armor66/LoRa-E77-GNSS/PCB/tBeacon_D2_mount.jpg

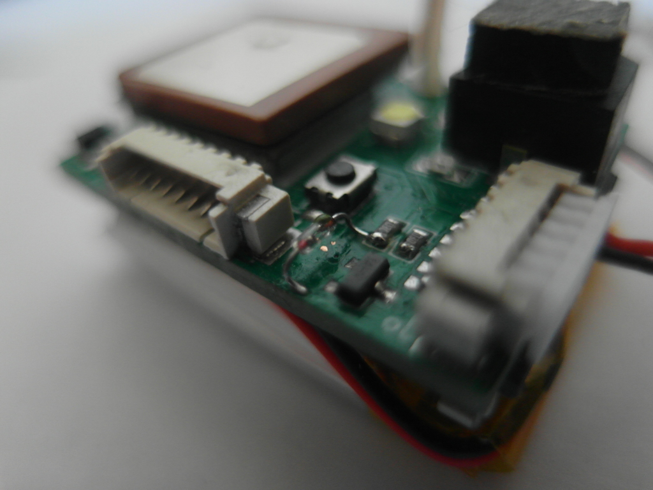
PCB/tBeacon_D2_mount.jpg
