armor66/LoRa-E77-GNSS/Photos/1.jpg

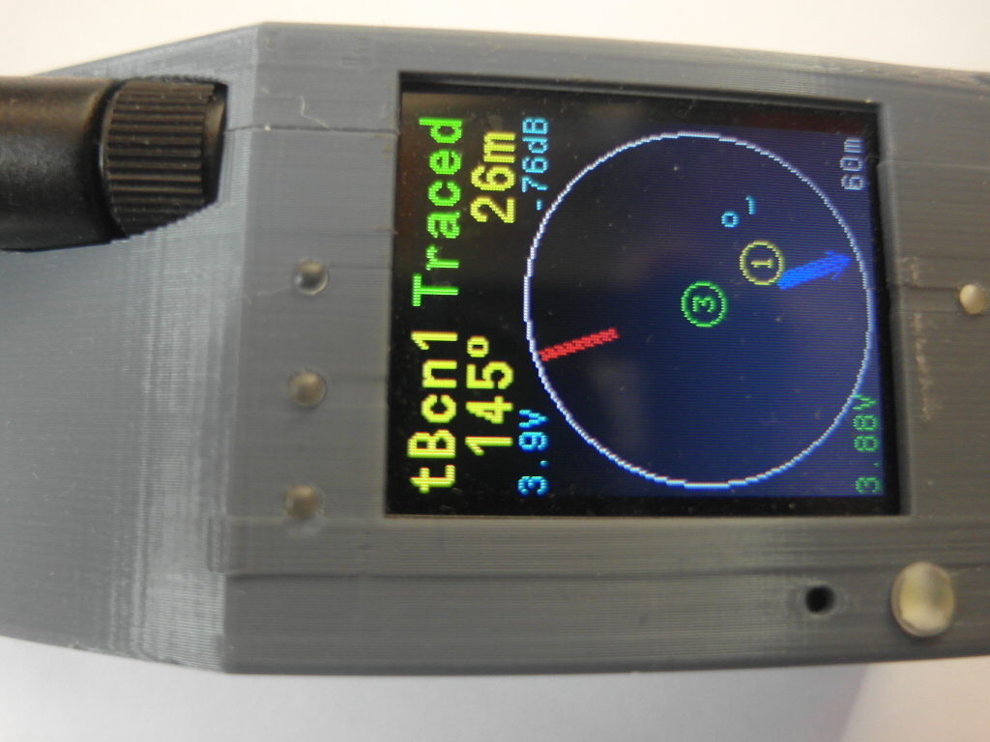
Photos/1.jpg
