armor66/LoRa-E77-GNSS/Photos/GPIO_Beacon.png

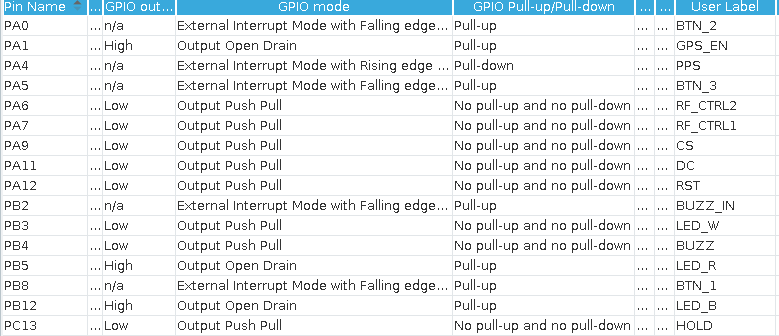
Photos/GPIO_Beacon.png
