armor66/LoRa-E77-GNSS/Photos/QUESCAN.jpg

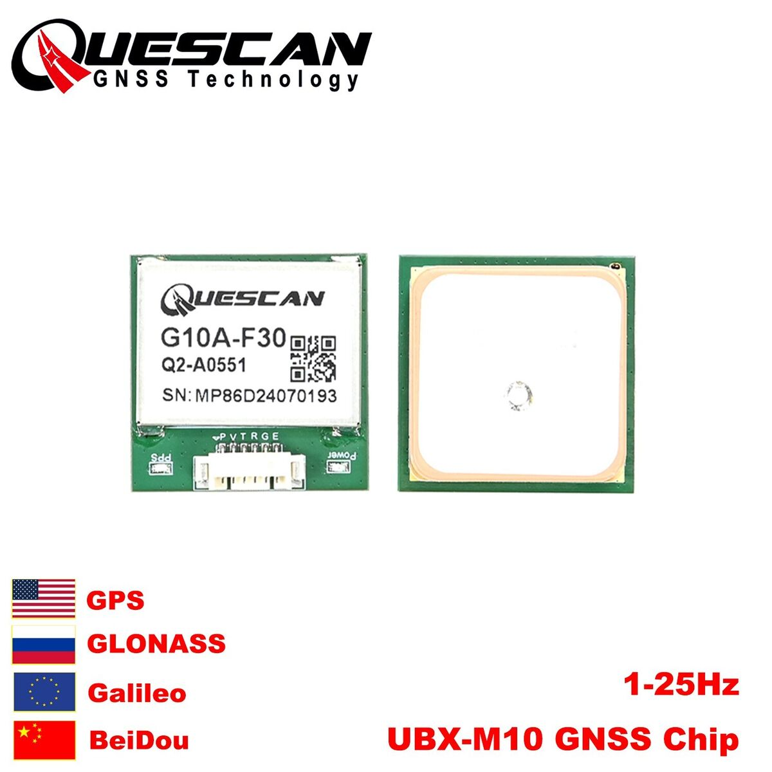
Photos/QUESCAN.jpg
