armor66/LoRa-E77-GNSS/E77-128x160/Core/Src/menu.c

#include <stdio.h>			//for 'sprintf'
#include <math.h>
#include "main.h"
#include "gpio.h"
#include "menu.h"
#include "buttons.h"
#include "tim.h"
#include "lptim.h"
#include "settings.h"
#include "compass.h"
#include "gnss.h"
#include "lrns.h"
#include "ds3231.h"

#include "lcd_display.h"

#define START_POS_GROUP		6

uint8_t get_current_item(void);
uint8_t get_last_item(void);
void set_current_item(uint8_t new_value);
void reset_current_item_in_menu(uint8_t menu);

void scroll_up(void);
void scroll_down(void);
void switch_forward(void);
void switch_backward(void);
// MAIN MENU
void draw_main(void);
//void main_ok(void);
// NAVIGATION MENU
//SUB NAVIGATION MENU
void draw_navigation(void);
void draw_beacons(void);
void navigation_up(void);
void navigation_down(void);
void navigation_ok(void);
//void navigation_esc(void);
void beacons_ok(void);
void beacons_esc(void);

void draw_navto_points(void);
void navto_points_ok(void);
void navto_points_esc(void);

// LAPS MENU
void draw_laps(void);
void new_laps(void);
void continue_laps(void);
// DEVICES MENU
void draw_devices(void);
void draw_this_device(void);
void draw_device_submenu(void);
void draw_set_points(void);
//SUB DEVICES MENU
void scroll_devices_up(void);
void scroll_devices_down(void);
void devices_ok(void);
void devices_esc(void);
// POINTS MENU
void draw_points(void);
void points_esc(void);
void draw_show_points(void);
void draw_clear_group(void);
void confirm_clear_group(void);
void draw_save_group(void);
void confirm_save_group(void);
void decline_save_group(void);
//SUB POINTS MENU
void set_subpoint_up(void);
void set_subpoint_down(void);
void set_subpoint_ok(void);
void set_subpoint_esc(void);
// SETTINGS MENU
void draw_settings(void);
void draw_set_settings(void);
//SUB SETTINGS MENU :0
void set_device_number_up(void);
void set_device_number_down(void);
void set_device_number_ok(void);
void set_device_number_esc(void);
//:1
void set_spreading_factor_up(void);
void set_spreading_factor_down(void);
void set_spreading_factor_ok(void);
void set_spreading_factor_esc(void);
//:2
void set_coding_rate_up(void);
void set_coding_rate_down(void);
void set_coding_rate_ok(void);
void set_coding_rate_esc(void);
//:3
void set_freq_channel_up(void);
void set_freq_channel_down(void);
void set_freq_channel_ok(void);
void set_freq_channel_esc(void);
//:4
void set_tx_power_up(void);
void set_tx_power_down(void);
void set_tx_power_ok(void);
void set_tx_power_esc(void);
//:5
void set_timezone_up(void);
void set_timezone_down(void);
void set_timezone_ok(void);
void set_timezone_esc(void);
//:6
void set_timeout_up(void);
void set_timeout_down(void);
void set_timeout_ok(void);
void set_timeout_esc(void);
//:7
void set_fence_up(void);
void set_fence_down(void);
void set_fence_ok(void);
void set_fence_esc(void);

// SAVE SETTINGS
void draw_confirm_settings(void);
void confirm_settings_reboot(void);
void donot_save_settings(void);
void confirm_erase_points(void);
void confirm_settings_restore(void);
//ACTIONS MENU
void draw_actions(void);
void power_long(void);
void actions_ok(void);
void actions_esc(void);
void draw_erase_points(void);
void draw_restore_defaults(void);

void draw_binding(void);
void confirm_binding(void);
void exit_binding(void);
void device_up(void);
void device_down(void);

void set_brightness(void);

//ALL MENUS HERE
enum    //menu number starts from 1, because 0 is used as "end marker" in menu structs
{
    M_MAIN = 1,
    M_NAVIGATION,
	M_BEACONS,

	M_LAPS,
	M_DEVICES,
	M_DEVICE_SUBMENU,
	M_SET_POINTS,

	M_NAVTO_POINTS,

	M_POINTS,
	M_POINTS_SUBMENU,
	M_CONFIRM_CLEARGROUP,
	M_CONFIRM_SAVEGROUP,

	M_SETTINGS,
	M_CONFIRM_SETTINGS,

	M_SET_DEVICE_NUMBER,
	M_SET_SPREADING_FACTOR,
	M_SET_CODING_RATE,
    M_SET_FREQ_CHANNEL,
    M_SET_TX_POWER,
	M_SET_TIMEZONE,
	M_SET_TIMEOUT,
	M_SET_FENCE,

	M_ACTIONS,
	M_ERASE_POINTS,
	M_CONFIRM_RESTORING,
	M_BINDING
};

//ALL MENU ITEMS HERE (for each menu separately)
//note: for all menus first item always has index of 0
#define M_ALL_I_FIRST (0)
//MAIN
enum
{
    M_MAIN_I_NAVIGATION = 0,
	M_MAIN_I_DEVICES,
	M_MAIN_I_NAVTO_POINTS,
	M_MAIN_I_POINTS,
	M_MAIN_I_SETTINGS,
	M_MAIN_I_ACTIONS,					//last item
    M_MAIN_I_LAST = M_MAIN_I_ACTIONS	//copy last item here
};
//DEVICE TO SAVE SUBMENU
enum
{
	M_DEVICE_SUBMENU_I_ALARMS = 0,
	M_DEVICE_SUBMENU_I_GROUP1,
	M_DEVICE_SUBMENU_I_GROUP2,
	M_DEVICE_SUBMENU_I_GROUP3,
	M_DEVICE_SUBMENU_I_GROUP4,
	M_DEVICE_SUBMENU_I_GROUP5,
	M_DEVICE_SUBMENU_I_BCNMAN,
	M_DEVICE_SUBMENU_I_LAST = M_DEVICE_SUBMENU_I_BCNMAN
};
//POINTS
enum
{
	M_POINTS_I_ALARMS = 0,
	M_POINTS_I_GROUP1,
	M_POINTS_I_GROUP2,
	M_POINTS_I_GROUP3,
	M_POINTS_I_GROUP4,
	M_POINTS_I_GROUP5,
	M_POINTS_I_BCNMAN,
	M_POINTS_I_SAVED1,
	M_POINTS_I_SAVED2,
	M_POINTS_I_SAVED3,
	M_POINTS_I_SAVED4,
	M_POINTS_I_SAVED5,
	M_POINTS_I_LAST = M_POINTS_I_SAVED5
};
//SETTINGS
enum
{
    M_SETTINGS_I_DEVICE = 0,
	M_SETTINGS_I_SPREADING_FACTOR,
	M_SETTINGS_I_CODING_RATE,
	M_SETTINGS_I_FREQ_CHANNEL,
	M_SETTINGS_I_TX_POWER,
	M_SETTINGS_I_TIMEZONE,
	M_SETTINGS_I_TIMEOUT,
	M_SETTINGS_I_FENCE,
    M_SETTINGS_I_LAST = M_SETTINGS_I_FENCE
};
//ACTIONS SUBMENU
enum
{
	M_ACTIONS_I_POWER_OFF = 0,
    M_ACTIONS_I_EMERGENCY,
	M_ACTIONS_I_ANTITHEFT,
	M_ACTIONS_I_BCNHALT,
	M_ACTIONS_I_BEEPER,
	M_ACTIONS_I_ERASE_POINTS,
	M_ACTIONS_I_SET_DEFAULTS,
	M_ACTIONS_I_FLWTREK,						//last item
	M_ACTIONS_I_LAST = M_ACTIONS_I_FLWTREK		//copy last item here
};
//Only exclusive (non default) actions here, for example edit a variable in settings
const struct
{
    uint8_t current_menu;
    uint8_t button_pressed;
    void (*execute_function)(void);
} menu_exclusive_table[] =
{
//  Current Menu                Button pressed          Action (function name)
//	{M_MAIN,					BTN_OK,					main_ok},
	{M_MAIN,					BTN_ESC,				set_brightness},

	{M_NAVIGATION,				BTN_UP,					navigation_up},		//change distance range
	{M_NAVIGATION,				BTN_DOWN,				navigation_down},	//change distance range
	{M_NAVIGATION,				BTN_OK,					navigation_ok},		//other points on loop
//	{M_NAVIGATION,				BTN_ESC,				navigation_esc},	//to main menu

	{M_BEACONS,					BTN_UP,					navigation_up},
	{M_BEACONS,					BTN_DOWN,				navigation_down},
	{M_BEACONS,					BTN_OK,					beacons_ok},
	{M_BEACONS,					BTN_ESC,				beacons_esc},

	{M_LAPS,					BTN_UP,					new_laps},
	{M_LAPS,					BTN_DOWN,				continue_laps},
	{M_LAPS,					BTN_OK,					draw_devices},
//	{M_LAPS,					BTN_ESC,				to M_MAIN},			//default action

	{M_DEVICES,					BTN_UP,					scroll_devices_up},
	{M_DEVICES,					BTN_DOWN,				scroll_devices_down},
	{M_DEVICES,					BTN_OK,					devices_ok},
	{M_DEVICES,					BTN_ESC,				devices_esc},

	{M_SET_POINTS,				BTN_UP,                 set_subpoint_up},
	{M_SET_POINTS,				BTN_DOWN,               set_subpoint_down},
	{M_SET_POINTS,				BTN_OK,                 set_subpoint_ok},
	{M_SET_POINTS,				BTN_ESC,            	set_subpoint_esc},

	{M_NAVTO_POINTS,			BTN_UP,					navigation_up},
	{M_NAVTO_POINTS,			BTN_DOWN,				navigation_down},
	{M_NAVTO_POINTS,			BTN_OK,					navto_points_ok},
	{M_NAVTO_POINTS,			BTN_ESC,				navto_points_esc},

	{M_SET_DEVICE_NUMBER,		BTN_UP,                 set_device_number_up},
	{M_SET_DEVICE_NUMBER,		BTN_DOWN,               set_device_number_down},
	{M_SET_DEVICE_NUMBER,		BTN_OK,                 set_device_number_ok},
	{M_SET_DEVICE_NUMBER,		BTN_ESC,            	set_device_number_esc},

	{M_SET_SPREADING_FACTOR,	BTN_UP,                 set_spreading_factor_up},
	{M_SET_SPREADING_FACTOR,	BTN_DOWN,               set_spreading_factor_down},
	{M_SET_SPREADING_FACTOR,	BTN_OK,                 set_spreading_factor_ok},
	{M_SET_SPREADING_FACTOR,	BTN_ESC,            	set_spreading_factor_esc},

	{M_SET_CODING_RATE,			BTN_UP,                 set_coding_rate_up},
	{M_SET_CODING_RATE,			BTN_DOWN,               set_coding_rate_down},
	{M_SET_CODING_RATE,			BTN_OK,                 set_coding_rate_ok},
	{M_SET_CODING_RATE,			BTN_ESC,            	set_coding_rate_esc},

	{M_SET_FREQ_CHANNEL,		BTN_UP,                 set_freq_channel_up},
	{M_SET_FREQ_CHANNEL,		BTN_DOWN,               set_freq_channel_down},
	{M_SET_FREQ_CHANNEL,		BTN_OK,                 set_freq_channel_ok},
	{M_SET_FREQ_CHANNEL,		BTN_ESC,            	set_freq_channel_esc},

	{M_SET_TX_POWER,			BTN_UP,                 set_tx_power_up},
	{M_SET_TX_POWER,			BTN_DOWN,               set_tx_power_down},
	{M_SET_TX_POWER,			BTN_OK,                 set_tx_power_ok},
	{M_SET_TX_POWER,			BTN_ESC,                set_tx_power_esc},

	{M_SET_TIMEZONE,			BTN_UP,					set_timezone_up},
	{M_SET_TIMEZONE,			BTN_DOWN,				set_timezone_down},
	{M_SET_TIMEZONE,			BTN_OK,					set_timezone_ok},
	{M_SET_TIMEZONE,			BTN_ESC,				set_timezone_esc},

	{M_SET_TIMEOUT,				BTN_UP,                 set_timeout_up},
	{M_SET_TIMEOUT,				BTN_DOWN,               set_timeout_down},
	{M_SET_TIMEOUT,				BTN_OK,                 set_timeout_ok},
	{M_SET_TIMEOUT,				BTN_ESC,            	set_timeout_esc},

	{M_SET_FENCE,				BTN_UP,                 set_fence_up},
	{M_SET_FENCE,				BTN_DOWN,               set_fence_down},
	{M_SET_FENCE,				BTN_OK,                 set_fence_ok},
	{M_SET_FENCE,				BTN_ESC,            	set_fence_esc},
	{M_CONFIRM_SETTINGS,		BTN_OK,					confirm_settings_reboot},
	{M_CONFIRM_SETTINGS,		BTN_ESC,				donot_save_settings},

	{M_MAIN,					BTN_PWR_LONG,			power_long},
	{M_NAVIGATION,				BTN_PWR_LONG,			power_long},
	{M_LAPS,					BTN_PWR_LONG,			power_long},
	{M_BEACONS,					BTN_PWR_LONG,			power_long},
	{M_DEVICES,					BTN_PWR_LONG,			power_long},
	{M_NAVTO_POINTS,			BTN_PWR_LONG,			power_long},
	{M_POINTS,					BTN_PWR_LONG,			power_long},
	{M_POINTS,					BTN_ESC,				points_esc},
	{M_POINTS_SUBMENU,			BTN_OK,					draw_clear_group},
	{M_CONFIRM_CLEARGROUP,		BTN_OK,					confirm_clear_group},
	{M_CONFIRM_SAVEGROUP,		BTN_UP,					set_subpoint_up},
	{M_CONFIRM_SAVEGROUP,		BTN_DOWN,				set_subpoint_down},
	{M_CONFIRM_SAVEGROUP,		BTN_OK,					confirm_save_group},
	{M_CONFIRM_SAVEGROUP,		BTN_ESC,				decline_save_group},
	{M_ACTIONS,					BTN_PWR_LONG,			power_long},
	{M_ACTIONS,					BTN_OK,					actions_ok},
	{M_ACTIONS,					BTN_ESC,				actions_esc},
//
	{M_ERASE_POINTS,			BTN_OK,					confirm_erase_points},
	{M_CONFIRM_RESTORING,		BTN_OK,					confirm_settings_restore},
	{M_BINDING,					BTN_UP,					device_up},
	{M_BINDING,					BTN_DOWN,				device_down},
	{M_BINDING,					BTN_OK,					confirm_binding},
	{M_BINDING,					BTN_ESC,				exit_binding},
    {0, 0, 0}   //end marker
};

//Default behavior (non exclusive) when OK button has been pressed (move forward)
const struct
{
    uint8_t current_menu;
    uint8_t current_item;
    uint8_t next_menu;
} menu_forward_table[] =
{
//  Current Menu                Current Item                		Next Menu
	{M_MAIN,  				M_MAIN_I_NAVIGATION,		M_NAVIGATION},
	{M_MAIN,    			M_MAIN_I_DEVICES,			M_LAPS},
//	{M_MAIN,    			M_MAIN_I_DEVICES,			M_DEVICES},
	{M_MAIN,    			M_MAIN_I_NAVTO_POINTS,		M_NAVTO_POINTS},
	{M_MAIN,    			M_MAIN_I_POINTS,			M_POINTS},
	{M_MAIN,    			M_MAIN_I_SETTINGS,			M_SETTINGS},
	{M_MAIN,    			M_MAIN_I_ACTIONS,			M_ACTIONS},

	{M_DEVICE_SUBMENU,		M_DEVICE_SUBMENU_I_ALARMS,			M_SET_POINTS},
	{M_DEVICE_SUBMENU,		M_DEVICE_SUBMENU_I_GROUP1,			M_SET_POINTS},
	{M_DEVICE_SUBMENU,		M_DEVICE_SUBMENU_I_GROUP2,			M_SET_POINTS},
	{M_DEVICE_SUBMENU,		M_DEVICE_SUBMENU_I_GROUP3,			M_SET_POINTS},
	{M_DEVICE_SUBMENU,		M_DEVICE_SUBMENU_I_GROUP4,	 		M_SET_POINTS},
	{M_DEVICE_SUBMENU,		M_DEVICE_SUBMENU_I_GROUP5,			M_SET_POINTS},
	{M_DEVICE_SUBMENU,		M_DEVICE_SUBMENU_I_BCNMAN,			M_SET_POINTS},

	{M_POINTS,				M_POINTS_I_ALARMS,				M_POINTS_SUBMENU},
	{M_POINTS,				M_POINTS_I_GROUP1,				M_POINTS_SUBMENU},
	{M_POINTS,				M_POINTS_I_GROUP2,			 	M_POINTS_SUBMENU},
	{M_POINTS,				M_POINTS_I_GROUP3,				M_POINTS_SUBMENU},
	{M_POINTS,				M_POINTS_I_GROUP4,				M_POINTS_SUBMENU},
	{M_POINTS,				M_POINTS_I_GROUP5,				M_POINTS_SUBMENU},
	{M_POINTS,				M_POINTS_I_BCNMAN,				M_POINTS_SUBMENU},
	{M_POINTS,				M_POINTS_I_SAVED1,				M_POINTS_SUBMENU},
	{M_POINTS,				M_POINTS_I_SAVED2,				M_POINTS_SUBMENU},
	{M_POINTS,				M_POINTS_I_SAVED3,				M_POINTS_SUBMENU},
	{M_POINTS,				M_POINTS_I_SAVED4,				M_POINTS_SUBMENU},
	{M_POINTS,				M_POINTS_I_SAVED5,				M_POINTS_SUBMENU},

	{M_SETTINGS,			M_SETTINGS_I_DEVICE,				M_SET_DEVICE_NUMBER},
	{M_SETTINGS,			M_SETTINGS_I_SPREADING_FACTOR,		M_SET_SPREADING_FACTOR},
	{M_SETTINGS,			M_SETTINGS_I_CODING_RATE,			M_SET_CODING_RATE},
	{M_SETTINGS,			M_SETTINGS_I_FREQ_CHANNEL,			M_SET_FREQ_CHANNEL},
	{M_SETTINGS,			M_SETTINGS_I_TX_POWER,				M_SET_TX_POWER},
	{M_SETTINGS,			M_SETTINGS_I_TIMEZONE,				M_SET_TIMEZONE},
	{M_SETTINGS,			M_SETTINGS_I_TIMEOUT,				M_SET_TIMEOUT},
	{M_SETTINGS,			M_SETTINGS_I_FENCE,					M_SET_FENCE},
    {0, 0, 0}   //end marker
};

//Default behavior (non exclusive) when ESC button has been pressed (move backward)
const struct
{
    uint8_t current_menu;
    uint8_t next_menu;
} menu_backward_table[] =
{
//  Current Menu                Next Menu
    {M_NAVIGATION,              M_MAIN},
	{M_BEACONS,					M_NAVIGATION},

	{M_LAPS,					M_MAIN},
	{M_DEVICES,                 M_MAIN},
	{M_DEVICE_SUBMENU,			M_DEVICES},
	{M_SET_POINTS,				M_DEVICE_SUBMENU},

	{M_NAVTO_POINTS,	        M_MAIN},

	{M_POINTS,	                M_MAIN},
	{M_POINTS_SUBMENU,			M_POINTS},
	{M_CONFIRM_CLEARGROUP,		M_POINTS_SUBMENU},
	{M_CONFIRM_SAVEGROUP,		M_NAVTO_POINTS},
//	{M_POINTS_SUBMENU_DEVICES,	M_POINTS},

    {M_SETTINGS,                M_CONFIRM_SETTINGS},	//M_MAIN},
	{M_CONFIRM_SETTINGS,		M_SETTINGS},
    {M_SET_DEVICE_NUMBER,       M_SETTINGS},
	{M_SET_SPREADING_FACTOR,	M_SETTINGS},
	{M_SET_CODING_RATE,			M_SETTINGS},
	{M_SET_FREQ_CHANNEL,		M_SETTINGS},
	{M_SET_TX_POWER,			M_SETTINGS},
	{M_SET_TIMEZONE,	        M_SETTINGS},
	{M_SET_TIMEOUT,				M_SETTINGS},
	{M_SET_FENCE,				M_SETTINGS},

	{M_ERASE_POINTS,			M_ACTIONS},
	{M_CONFIRM_RESTORING,		M_ACTIONS},
	{M_BINDING,					M_ACTIONS},
    {0, 0}      //end marker
};
//Structure with list of menus and real-time values of current item in current menu. Last Item is needed for scroll function
//note: if current menu has no items (like INFO menu) no need to put it in structure below,
//because item functions (get, get last, set) automatically return 0 (which is zero item)
struct
{
    const uint8_t curent_menu;
    uint8_t cur_item;
    const uint8_t last_item;
} item_table[] =
{
//  Current Menu                Current Item                Last Item in Current Menu
    {M_MAIN,                    M_ALL_I_FIRST,              M_MAIN_I_LAST},
	{M_DEVICE_SUBMENU,			M_ALL_I_FIRST,				M_DEVICE_SUBMENU_I_LAST},
	{M_POINTS, 	                M_ALL_I_FIRST,              M_POINTS_I_LAST},
    {M_SETTINGS,                M_ALL_I_FIRST,              M_SETTINGS_I_LAST},
	{M_ACTIONS,					M_ALL_I_FIRST,				M_ACTIONS_I_LAST},
    {0, 0, 0}   //end marker
};

//List of menus with appropriate functions to draw it (show on screen)
const struct
{
    uint8_t current;
    void (*action)(void);
} menu_draw_table[] =
{
//  Current Menu                Draw Function
	{M_MAIN,                    draw_main},

	{M_NAVIGATION,				draw_navigation},
	{M_BEACONS,					draw_beacons},

	{M_LAPS,                 	draw_laps},
	{M_DEVICES,                 draw_devices},			//can be commented
	{M_DEVICE_SUBMENU,     		draw_device_submenu},
	{M_SET_POINTS,				draw_set_points},

	{M_NAVTO_POINTS,			draw_navto_points},

	{M_POINTS,                  draw_points},
	{M_POINTS_SUBMENU,			draw_show_points},
	{M_CONFIRM_SAVEGROUP,		draw_save_group},

    {M_SETTINGS,                draw_settings},
    {M_SET_DEVICE_NUMBER,		draw_set_settings},
	{M_SET_SPREADING_FACTOR,	draw_set_settings},
	{M_SET_CODING_RATE,			draw_set_settings},
	{M_SET_FREQ_CHANNEL,		draw_set_settings},
	{M_SET_TX_POWER,			draw_set_settings},
    {M_SET_TIMEZONE,			draw_set_settings},
	{M_SET_TIMEOUT,				draw_set_settings},
	{M_SET_FENCE,				draw_set_settings},
	{M_CONFIRM_SETTINGS,		draw_confirm_settings},

	{M_ACTIONS,					draw_actions},
	{M_ERASE_POINTS,			draw_erase_points},
	{M_CONFIRM_RESTORING,		draw_restore_defaults},
	{M_BINDING,					draw_binding},
    {0, 0}      //end mark
};

//#define PVTsize 100
//uint8_t PVTbuffer[PVTsize] = {0};
char string_buffer[20][27];		//15raws,22(~240:11)items
char *fixType[] = {"NoFix", "DReck", "2DFix", "3DFix", "DReck", "Time"}; 	//only 2 bits used to transmit (first 4 items)

//int8_t main_flags.current_point_group = 0;		//Current number of memory point to save
uint8_t current_mem_subpoint = 0;
uint8_t points_group_ind = 0;						//NavTo Points begins from Start Positions group
uint8_t memory_subpoint = 0;
uint8_t memory_subpoint_ind[MEMORY_POINT_GROUPS];
uint8_t flag_group_has_changed[MEMORY_POINT_GROUPS];

int16_t north = 0;
int16_t north_old = 0;
int16_t azimuth_relative_deg = 0;
int16_t scaled_dist;
int16_t distance_old[10];
double north_rad = 0;
double north_rad_old = 0;
double azimuth_relative_rad;
double azimuth_relative_rad_old[10];

int8_t row;
int8_t this_device;								//device number of this device, see init_menu()
//int8_t current_device;

int8_t current_menu;
uint8_t return_from_power_menu; 							//Menu to return to after exit from power menu. Power menu can be accessed from different menus, therefore we have to store menu to return.
uint8_t return_from_points_menu;
uint8_t flag_settings_changed = 0;

uint8_t *p_coding_rate_values;
uint8_t *p_tx_power_values;

uint16_t range = 30;
uint8_t range_ind = 0;
uint8_t range_scale[] = {1, 2, 4, 8, 16, 32, 64};

int8_t previous_menu;		//to return if start point not saved
int8_t firstFreeStartPoint;	//for save_start_pos()
int8_t ind = 0;				//out of the function draw_navto_points() to roll up if points > 3
int8_t startHour;
int8_t startMinute;
int8_t startSecond;
int8_t lapsSaved;
int8_t lapsPaused;
int8_t lapsCounter;
uint16_t lapsTimeSaved;
uint16_t lapsDistSaved;

struct devices_struct **pp_devices_menu;
struct point_groups_struct **pp_point_groups_menu;
struct points_struct **pp_points_menu;

struct settings_struct *p_settings_menu;
struct settings_struct settings_copy_menu;

ds3231_time_t *p_timeData;

void init_menu(void)
{
	//Load all devices
	pp_devices_menu = get_devices();
	pp_point_groups_menu = get_point_groups();
	pp_points_menu = get_points();
	//Load settings and create a local copy
	p_settings_menu = get_settings();
	settings_copy_menu = *p_settings_menu;
	main_flags.binding_device = main_flags.current_device = this_device = p_settings_menu->device_number;

	p_coding_rate_values = get_coding_rate_values();
	p_tx_power_values = get_tx_power_values();

	p_timeData = get_timeData();

	current_menu = M_MAIN;
//	return_from_power_menu = M_MAIN;
	set_current_item(M_MAIN_I_NAVIGATION);

	main_flags.display_status = 1;
	main_flags.update_screen = 1;
	main_flags.brightness = 16;
	lptim1_start(16, main_flags.brightness);
/* first position to save when first_time_locked after power on */
	memory_subpoint_ind[START_POS_GROUP] = 1;
	main_flags.binding_sf = p_settings_menu->spreading_factor;
}

void set_brightness(void)
{
	if(main_flags.brightness == 16)
	{
		main_flags.brightness = 11;
	}else if(main_flags.brightness == 11)
	{
		main_flags.brightness = 0;
	}else
	{
		main_flags.brightness = 16;
	}
	lptim1_start(16, main_flags.brightness);
}

//Check for buttons and change menu if needed
void change_menu(uint8_t button_code)
{
	if((current_menu == M_LAPS) && (lapsCounter) && (button_code > 2))	//should respond any except BTN_PWR
	{
		lptim1_start(16, main_flags.brightness);
		main_flags.display_status = 1;
	}

	int8_t point_absolute_index = 0;
	if(main_flags.display_status)	//if lcd is on
	{	//search for exclusive operation(function) for this case
		for (uint8_t i = 0; menu_exclusive_table[i].current_menu; i++)     //until end marker
		{
			if (current_menu == menu_exclusive_table[i].current_menu &&
				button_code == menu_exclusive_table[i].button_pressed)
			{
				fill_screen(BLACK);
				menu_exclusive_table[i].execute_function();
				return;         //exit
			}
		}
//there is no exclusive operations for that case, perform default action
		switch (button_code)
		{
			case BTN_UP:
				scroll_up();
				break;

			case BTN_DOWN:
				scroll_down();
				break;

			case BTN_OK:
				switch_forward();
				fill_screen(BLACK);
				break;

			case BTN_ESC:
				switch_backward();
				fill_screen(BLACK);
				break;

			case BTN_PWR:
				lptim1_stop();							//lcd_off
				main_flags.display_status = 0;			//do not draw or change menu
				main_flags.current_point_group = 0;		//to start save or erase points from group 1
				break;

			default:
				break;
		}	//switch (button_code)
	}else 	//if lcd is off, display_status = 0
	{
		switch (button_code)
		{
			case BTN_PWR_LONG:
				lptim1_start(16, main_flags.brightness);
				main_flags.display_status = 1;
				if(current_menu == M_NAVIGATION && pp_devices_menu[this_device]->valid_fix_flag && pp_devices_menu[this_device]->flwtrek_flag)
				{
					main_flags.find_nearest_trekpoint_flag = 1;		//find_nearest_trekpoint();
					fill_screen(BLACK);
				}
				break;

			case BTN_UP:				//if short pressed
				timer16_start();		//hold 1.5 second for next short press

				if(main_flags.current_point_group < 5) {
					main_flags.current_point_group++;
					memory_subpoint_ind[main_flags.current_point_group] = 0;	//to start from point 1
//					led_blue_on();		//main_flags.current_point_group has set
				}else {
					shortBeeps(2);			//if(main_flags.current_point_group == 5)
					main_flags.current_point_group = 0;
//					led_blue_off();		//main_flags.current_point_group has reseted
				}
				break;		//leave case BTN_UP

			case BTN_OK:			//if long pressed && (main_flags.current_point_group > 0))
				timer16_stop();		//stop before IRQ and clear current_point_group

				if(!pp_devices_menu[this_device]->valid_fix_flag) {
					shortBeeps(2);			//if no valid_fix_flag when attempt to save point
					main_flags.current_point_group = 0;
//					led_blue_off();		//main_flags.current_point_group has reseted
					break;		//leave case BTN_OK
				}
				if(main_flags.current_point_group > 0) {
					longBeeps(main_flags.current_point_group);
				}else break;	//leave case BTN_OK

				do{
					memory_subpoint_ind[main_flags.current_point_group]++;
					if(memory_subpoint_ind[main_flags.current_point_group] == MEMORY_SUBPOINTS)
					{
						memory_subpoint_ind[main_flags.current_point_group] = 0;							//exist_flag always == 0
						pp_points_menu[main_flags.current_point_group * MEMORY_SUBPOINTS]->exist_flag = 0;	//clear subpoint 0
					}
					point_absolute_index = main_flags.current_point_group * MEMORY_SUBPOINTS + memory_subpoint_ind[main_flags.current_point_group];
				} while (pp_points_menu[point_absolute_index]->exist_flag);		// == 1

				if(memory_subpoint_ind[main_flags.current_point_group] == 0)
				{
					main_flags.current_point_group = 0;
//					led_blue_off();		//main_flags.current_point_group has reseted
					break;			//longBeeps(main_flags.current_point_group) and leave case BTN_OK
				}

				save_one_point(point_absolute_index);
				points_group_save(main_flags.current_point_group);

				shortBeeps(1);	//memory_subpoint_ind[main_flags.current_point_group]);	//number of point to save

				fill_screen(BLACK);
//				return_from_points_menu = current_menu;
				current_menu = M_POINTS;
				set_current_item(main_flags.current_point_group);
				main_flags.current_point_group = 0;
//				led_blue_off();		//main_flags.current_point_group has reseted
				break;		//leave case BTN_OK

			case BTN_DOWN:				//if short pressed
				timer16_start();		//hold 1.5 second for next short press

				if(main_flags.current_point_group < 7) {			//5 groups + beacon + 1 for all devices
					main_flags.current_point_group++;
//					led_blue_on();		//main_flags.current_point_group has set
				}else {
					shortBeeps(2);			//if(main_flags.current_point_group == 12)
					main_flags.current_point_group = 0;
//					led_blue_off();		//main_flags.current_point_group has reseted
				}
				break;		//leave case BTN_DOWN

			case BTN_ESC:		//if long pressed && (main_flags.current_point_group > 0))
				timer16_stop();		//stop before IRQ and clear current_point_group

				if(main_flags.current_point_group > 0)
				{
					longBeeps(main_flags.current_point_group);
//					shortBeeps(1);							//just for notice instead of actual long beeps
				}else break;	//leave case BTN_ESC

				if(main_flags.current_point_group < 7)			//5 groups + beacon
				{
/*as in "confirm_clear_group(void)" function*/
					clear_points_group(main_flags.current_point_group);
					int8_t ind;
					for(uint8_t sub_point = 0; sub_point < MEMORY_SUBPOINTS; sub_point++)
					{
						ind = (main_flags.current_point_group * MEMORY_SUBPOINTS) + sub_point;
						pp_points_menu[ind]->exist_flag = 0;
					}
					saved_group_load(main_flags.current_point_group);
				}

				if(main_flags.current_point_group == 7)			//for all devices
				{
					erase_saved_devices();

					for(uint8_t i = 57; i < 96; i++)	//57 to 96: 8 for saved device each
					{
						pp_points_menu[i]->exist_flag = 0;
					}

					for(uint8_t i = 1; i < (DEVICES_ON_AIR_MAX+1); i++)
					{
						lost_device_load(i);
					}
				}

/******************************************/
				fill_screen(BLACK);
//				return_from_points_menu = current_menu;
				current_menu = M_POINTS;
				set_current_item(main_flags.current_point_group);
				main_flags.current_point_group = 0;
//				led_blue_off();		//main_flags.current_point_group has reseted
				break;		//leave case BTN_ESC

			default:
				main_flags.current_point_group = 0;
//				led_blue_off();		//main_flags.current_point_group has reseted
				break;
		}	//switch (button_code)
	}		//if lcd is off
}	//change_menu
//Scroll current menu Up
void scroll_up(void)
{
    uint8_t current = get_current_item();
    uint8_t last = get_last_item();

    if (current == M_ALL_I_FIRST)
    {
        set_current_item(last);
    }
    else
    {
        set_current_item(current - 1);
    }
}
//Scroll current menu Down
void scroll_down(void)
{
    uint8_t current = get_current_item();
    uint8_t last = get_last_item();

    if (current == last)
    {
        set_current_item(M_ALL_I_FIRST);
    }
    else
    {
        set_current_item(current + 1);
    }
}
//Switch menu forward by default
void switch_forward(void)
{
    for (uint8_t i = 0; menu_forward_table[i].current_menu; i++)
    {
        if (current_menu == menu_forward_table[i].current_menu &&
            get_current_item() == menu_forward_table[i].current_item)
        {
            current_menu = menu_forward_table[i].next_menu;
            break;
        }
    }
}
//Switch menu backward by default
void switch_backward(void)
{
    for (uint8_t i = 0; menu_backward_table[i].current_menu; i++)
    {
        if (current_menu == menu_backward_table[i].current_menu)
        {
            set_current_item(M_ALL_I_FIRST);        //reset current item before exit
            current_menu = menu_backward_table[i].next_menu;
            break;
        }
    }
}
//Get currently selected item in current menu
uint8_t get_current_item(void)
{
    for (uint8_t i = 0; item_table[i].curent_menu; i++)
    {
        if (current_menu == item_table[i].curent_menu)
        {
            return item_table[i].cur_item;
        }
    }
    return 0;       //automatically return 0 if item not found in item_table[]
}
//Get last item in current menu
uint8_t get_last_item(void)
{
    for (uint8_t i = 0; item_table[i].curent_menu; i++)
    {
        if (current_menu == item_table[i].curent_menu)
        {
            return item_table[i].last_item;
        }
    }
    return 0;       //automatically return 0 if item not found in item_table[]
}
//Set item to be current in current menu
void set_current_item(uint8_t new_value)
{
    for (uint8_t i = 0; item_table[i].curent_menu; i++)
    {
        if (current_menu == item_table[i].curent_menu)
        {
            item_table[i].cur_item = new_value;
            break;
        }
    }
}
//Reset item in any menu
void reset_current_item_in_menu(uint8_t menu)
{
    for (uint8_t i = 0; item_table[i].curent_menu; i++)
    {
        if (menu == item_table[i].curent_menu)
        {
            item_table[i].cur_item = M_ALL_I_FIRST;
            break;
        }
    }
}
//------------------------------------------------------------------
//--------------------------- DRAW -----------------------------
//Draw current menu
void draw_current_menu(void)
{
	if(main_flags.display_status)	//if lcd is on
	{
		for (uint8_t i = 0; menu_draw_table[i].current; i++)
		{
			if (current_menu == menu_draw_table[i].current)
			{
				menu_draw_table[i].action();
				break;
			}
		}
	}
//	else if(!IS_BEACON)	//if display has not lit, if IS_BEACON do nothing
//	{
		for(int8_t i = 1; i < 1 + p_settings_menu->devices_on_air; i++)
		{
			if(i != this_device)
			{
				if(pp_devices_menu[i]->emergency_flag)	// || pp_devices_menu[i]->antitheft_flag)
				{
//					fill_screen(BLACK);
					lptim1_start(16, main_flags.brightness);
					main_flags.display_status = 1;
//todo go to alarm point while display_status==0
//					points_group_ind = 0;
//					draw_navto_points();			//to draw immediately
//					current_menu = M_NAVTO_POINTS;	//do not return previous menu
				}
			}
		}
//	}
}
//------------------------------------------------------------------
//---------------------------MAIN MENU------------------------------

void draw_main(void)
{
	uint8_t day;	// = PVTbuffer[7+6];
//	uint8_t month = PVTbuffer[6+6];
	uint8_t year;	// = (PVTbuffer[5+6]<<8) + PVTbuffer[4+6];
	int8_t hour;	// = PVTbuffer[14];
	row = 0;

	if(main_flags.rtc_enabled || main_flags.fix_valid)
//(pp_devices_menu[this_device]->valid_date_flag)	//bit 5: information about UTC Date and Time of Day validity conﬁrmation is available
	{
		year = (uint8_t)(p_timeData->year - 2000);
		hour = p_timeData->hour + p_settings_menu->time_zone_hour;
		if(hour > 23)
		{
			hour = hour - 24;
			day = 1 + p_timeData->date;
		}
		else day = p_timeData->date;
	}
	else day = year = hour = 0;

	if(pp_devices_menu[this_device]->batt_voltage < 50)		// U < 3.2volt (!pp_devices_menu[this_device]->batt_voltage)
	{
		sprintf(&string_buffer[row][0], "DevID:%02d Batt low!", this_device);
		draw_str_by_rows(0, 1+row*11, &string_buffer[row][0], &Font_7x9, ORANGE,BLACK);
	}else
	{
		sprintf(&string_buffer[row][0], "DevID:%d/%d %d.%02dVolt", this_device, p_settings_menu->devices_on_air,
			(pp_devices_menu[this_device]->batt_voltage+270)/100,
			(pp_devices_menu[this_device]->batt_voltage+270)%100);
		draw_str_by_rows(0, 1+row*11, &string_buffer[row][0], &Font_7x9, WHITE,BLACK);
	}
	row+=1;	//1
	if(main_flags.rtc_enabled || main_flags.fix_valid)
	{
		(sprintf(&string_buffer[row][0], "%02d/%02d/%02d  %02d:%02d:%02d",
			day, p_timeData->month, year, hour, p_timeData->minute, p_timeData->second));
		(main_flags.fix_valid)?
				draw_str_by_rows(0, 1+row*11, &string_buffer[row][0], &Font_7x9, WHITE,BLACK):
				draw_str_by_rows(0, 1+row*11, &string_buffer[row][0], &Font_7x9, CYAN,BLACK);
	}else
	{
		(sprintf(&string_buffer[row][0], "RTC IS NOT APPLIED"));
		draw_str_by_rows(0, 1+row*11, &string_buffer[row][0], &Font_7x9, ORANGE,BLACK);
	}
//	for (uint8_t k = 0; k < row+1; k++)
//	{
//		draw_str_by_rows(0, 1+k*11, &string_buffer[k][0], &Font_7x9, WHITE,BLACK);
//	}
	row+=1;	//2
	if(main_flags.nav_pvt_ram_flag)
	{
		sprintf(&string_buffer[row][0], "%d %5s pDop:%2d.%02d", main_flags.fix_valid, fixType[pp_devices_menu[this_device]->fix_type_opt],
						pp_devices_menu[this_device]->p_dop/100, pp_devices_menu[this_device]->p_dop%100);
		(pp_devices_menu[this_device]->valid_fix_flag)?
				draw_str_by_rows(0, 1+row*11, &string_buffer[row][0], &Font_7x9, WHITE,BLACK):
//				draw_str_by_rows(0, 1+row*11, &string_buffer[row][0], &Font_7x9, CYAN,BLACK);
				((main_flags.GPScold_restarted)?
						draw_str_by_rows(0, 1+row*11, &string_buffer[row][0], &Font_7x9, ORANGE,BLACK):
						draw_str_by_rows(0, 1+row*11, &string_buffer[row][0], &Font_7x9, CYAN,BLACK));
	}
	else draw_str_by_rows(0, 1+row*11, "GPS not configured", &Font_7x9, ORANGE,BLACK);

	row+=1;	//3
	int8_t dev;
	for(dev = 1; dev < 1 + p_settings_menu->devices_on_air; dev++)
	{
		if(dev != this_device)
		{
			if(pp_devices_menu[dev]->emergency_flag)	// || (dev == p_settings_menu->devices_on_air))		//do not exceed devices_max
			{
				break;
			}
			else if(pp_devices_menu[dev]->antitheft_flag)
			{
				break;
			}
			else if(pp_devices_menu[dev]->bcntohalt_flag)
			{
				break;
			}
		}
		if(dev == p_settings_menu->devices_on_air)		//do not exceed devices_max and if this_device
		{
			dev = 0;
			break;
		}
	}

	if(pp_devices_menu[dev]->emergency_flag)
	{
		sprintf(&string_buffer[row][0], "Dev%d set EMERGENCY", dev);
		draw_str_by_rows(0, 1+row*11, &string_buffer[row][0], &Font_7x9, CYAN,BLACK);
	}
	else if(pp_devices_menu[dev]->antitheft_flag)
	{
		sprintf(&string_buffer[row][0], "Bcn%d AntiTheftMode", dev);
		draw_str_by_rows(0, 1+row*11, &string_buffer[row][0], &Font_7x9, CYAN,BLACK);
	}
	else if(pp_devices_menu[dev]->bcntohalt_flag)
	{
		sprintf(&string_buffer[row][0], "Bcn%d HaltModeReady", dev);
		draw_str_by_rows(0, 1+row*11, &string_buffer[row][0], &Font_7x9, CYAN,BLACK);
	}
	else
	{
		int8_t nods_on_the_air = (pp_devices_menu[1]->valid_fix_flag) + (pp_devices_menu[2]->valid_fix_flag) + (pp_devices_menu[3]->valid_fix_flag) +
																		(pp_devices_menu[4]->valid_fix_flag) + (pp_devices_menu[5]->valid_fix_flag);
		sprintf(&string_buffer[row][0], "OnTheAir: %d/%d Devs", nods_on_the_air, p_settings_menu->devices_on_air);
		draw_str_by_rows(0, 1+row*11, &string_buffer[row][0], &Font_7x9, WHITE,BLACK);
	}

	sprintf(&string_buffer[2][0], " Navigation");
	sprintf(&string_buffer[3][0], " Devices   ");
	sprintf(&string_buffer[4][0], " Nav2points");
	sprintf(&string_buffer[5][0], " Points    ");
	sprintf(&string_buffer[6][0], " Settings  ");
	sprintf(&string_buffer[7][0], " Actions   ");
	row = 2 + get_current_item();
	for (uint8_t k = 2; k < 8; k++)
	{
		if(k == row) draw_str_by_rows(3, 10+k*19, &string_buffer[k][0], &Font_11x18, YELLOW,BLACK);
		else draw_str_by_rows(3, 10+k*19, &string_buffer[k][0], &Font_11x18, GREEN,BLACK);
	}
//	draw_char(3, 10+row*19, *">", &Font_11x18, YELLOW,BLACK);	//">"
	int8_t slot = main_flags.time_slot + 1;
	if(main_flags.time_slot == p_settings_menu->devices_on_air) slot = 1;
	if((p_settings_menu->spreading_factor == 12) && (main_flags.time_slot == 2)) slot = 1;
	sprintf(&string_buffer[row][0], "%d",slot);
	draw_str_by_rows(3, 10+row*19,  &string_buffer[row][0], &Font_11x18, YELLOW,BLACK);
}
//--------------------------------MAIN MENU END------------------------------
//----------------------------------------------------------------------------
//--------------------------------NAVIGATION MENU--------------------------------
void draw_navigation(void)	//int8_t menu)
{
	row = 0;
	uint8_t dev = 0;

	if(pp_devices_menu[this_device]->gps_speed > GPS_SPEED_THRS)
	{
		sprintf(&string_buffer[row][4], "%2dkmh", pp_devices_menu[this_device]->gps_speed);
		draw_str_by_rows(37, row*19, &string_buffer[row][4], &Font_11x18, GREEN,BLACK);
	 	(heading_deg < 100)? (sprintf(&string_buffer[row+=1][4], "%3d%% ", heading_deg)): (sprintf(&string_buffer[row+=1][4], " %3d%%", heading_deg));	//just shift->
	 	draw_str_by_rows(37, (row)*19, &string_buffer[row][4], &Font_11x18, YELLOW,BLACK);
	}else if(is_north_ready())
	{
		draw_str_by_rows(37, row*19, " Magn", &Font_11x18, CYANB,BLACK);
	 	(heading_deg < 100)? (sprintf(&string_buffer[row+=1][4], "%3d%% ", heading_deg)): (sprintf(&string_buffer[row+=1][4], " %3d%%", heading_deg));	//just shift->
	 	draw_str_by_rows(37, (row)*19, &string_buffer[row][4], &Font_11x18, GREEN,BLACK);
	}else
	{
		draw_str_by_rows(37, row*19, " TURN", &Font_11x18, RED,BLACK);
		draw_str_by_rows(37, (row+=1)*19, " ARND", &Font_11x18, RED,BLACK);
	}

	if(is_north_ready())
	{
		(heading_rad < 0)? (north_rad = -heading_rad): (north_rad = 2*M_PI - heading_rad);
		draw_arrow(63, 97, 57, north_rad_old, 28, BLACK, BLACK);
		draw_arrow(63, 97, 57, north_rad, 28, CYANB, RED);
		north_rad_old = north_rad;
	}else draw_arrow(63, 97, 57, north_rad_old, 28, BLACK, BLACK);

	for(dev = 1; dev < (p_settings_menu->devices_on_air + 1); dev++)
	{
		if(dev != this_device)
		{
			if(pp_devices_menu[dev]->valid_fix_flag) break;
		}
		if(dev == p_settings_menu->devices_on_air)
		{
			dev = 0;		//if no "valid_fix_flag" received
			break;			//do not exceed "devices_on_air" on exit
		}
	}

	pp_devices_menu[dev]->beacon_flag? sprintf(&string_buffer[0][0], "Bcn:%d", dev): sprintf(&string_buffer[0][0], "Dev:%d", dev);	//if is beacon

//ext	azimuth_relative_deg = azimuth_deg_signed[dev] - heading_deg;
		azimuth_relative_deg = pp_devices_menu[dev]->azimuth_deg_signed - heading_deg;
		if(azimuth_relative_deg > 180) azimuth_relative_deg -= 360;
		if(azimuth_relative_deg < -180) azimuth_relative_deg += 360;
		sprintf(&string_buffer[1][0], "%4d%%", azimuth_relative_deg);
//ext	sprintf(&string_buffer[2][0], "%4dm", ((uint16_t)distance[dev] & 0x1FFF));
		sprintf(&string_buffer[2][0], "%4dm", ((uint16_t)pp_devices_menu[dev]->distance & 0x1FFF));
		sprintf(&string_buffer[3][0], "%4ddB", pp_devices_menu[dev]->rssi);		//(int8_t)buffer[BUFFER_AIR_SIZE]);

		for (uint8_t k = 0; k < 4; k++) {
			if(pp_devices_menu[dev]->valid_fix_flag) draw_str_by_rows(0, k*11, &string_buffer[k][0], &Font_7x9, YELLOW,BLACK);		//if remote fix valid (validFixFlag[dev])
			else draw_str_by_rows(0, k*11, &string_buffer[k][0], &Font_7x9, MAGENTA,BLACK);
		}

	for(dev = p_settings_menu->devices_on_air; dev > 0; dev--)
	{
		if(dev != this_device)
		{
			if(pp_devices_menu[dev]->valid_fix_flag) break;
		}
	}

	pp_devices_menu[dev]->beacon_flag? sprintf(&string_buffer[0][13], "Bcn:%d", dev): sprintf(&string_buffer[0][13], "Dev:%d", dev);	//if is beacon

//ext	azimuth_relative_deg = azimuth_deg_signed[dev] - heading_deg;
		azimuth_relative_deg = pp_devices_menu[dev]->azimuth_deg_signed - heading_deg;
		if(azimuth_relative_deg > 180) azimuth_relative_deg -= 360;
		if(azimuth_relative_deg < -180) azimuth_relative_deg += 360;

		sprintf(&string_buffer[1][13], "%4d%%", azimuth_relative_deg);
//ext	sprintf(&string_buffer[2][13], "%4dm", ((uint16_t)distance[dev] & 0x1FFF));
		sprintf(&string_buffer[2][13], "%4dm", ((uint16_t)pp_devices_menu[dev]->distance & 0x1FFF));
		sprintf(&string_buffer[3][13], "%4dd", pp_devices_menu[dev]->rssi);		//(int8_t)buffer[BUFFER_AIR_SIZE]);

		for (uint8_t k = 0; k < 4; k++) {
			if(pp_devices_menu[dev]->valid_fix_flag) draw_str_by_rows(91, k*11, &string_buffer[k][13], &Font_7x9, YELLOW,BLACK);		//if remote fix valid (validFixFlag[dev])
			else draw_str_by_rows(91, k*11, &string_buffer[k][13], &Font_7x9, MAGENTA,BLACK);
		}

	if(pp_devices_menu[this_device]->valid_fix_flag && pp_devices_menu[this_device]->flwtrek_flag)
	{
		manage_trekpoints(range_ind);
	}

	for(uint8_t i = 0; i < (p_settings_menu->devices_on_air + 1); i++) {
		if(i == this_device) {										//if this device
			draw_position(63, 97, 0, 0, 7, i, GREEN);
		}
		else if (pp_devices_menu[i]->valid_fix_flag) {									//if remote fix valid
//ext		scaled_dist = ((int16_t)distance[i] & 0x1FFF)*2  / range_scale[range_ind];
			scaled_dist = ((int16_t)pp_devices_menu[i]->distance & 0x1FFF)*2  / range_scale[range_ind];
//ext		azimuth_relative_rad = azimuth_rad[i] - heading_rad;
			azimuth_relative_rad = pp_devices_menu[i]->azimuth_rad - heading_rad;
			erase_position(63, 97, distance_old[i], azimuth_relative_rad_old[i], 8);
			if(scaled_dist > range * 2)
			{
				scaled_dist = range * 2;
				draw_position(63, 97, scaled_dist, azimuth_relative_rad, 7, i, RED);
			}else draw_position(63, 97, scaled_dist, azimuth_relative_rad, 7, i, YELLOW);
			distance_old[i] = scaled_dist;
			azimuth_relative_rad_old[i] = azimuth_relative_rad;
		}
		else if(distance_old[i] > 3) erase_position(63, 97, distance_old[i], azimuth_relative_rad_old[i], 8);	//erase or change CYAN to MAGENTA
	}

	draw_circle(63, 97, 60, WHITE);
	row = 13;
	sprintf(&string_buffer[row][0], "%d.%02dV", (pp_devices_menu[this_device]->batt_voltage+270)/100,
		  	   	   	   	   	    		 (pp_devices_menu[this_device]->batt_voltage+270)%100);
	draw_str_by_rows(0, 7+row*11, &string_buffer[row][0], &Font_7x9, GREEN,BLACK);
	sprintf(&string_buffer[row][13], "%4dm", range * range_scale[range_ind]);
	draw_str_by_rows(92, 7+row*11, &string_buffer[row][13], &Font_7x9, WHITE,BLACK);
}
void draw_beacons(void)
{
	if(main_flags.current_device == this_device) main_flags.current_device++;
	if(main_flags.current_device > p_settings_menu->devices_on_air) main_flags.current_device = 1;

	row = 0;
	uint8_t beacons_group_start = (MEMORY_POINT_GROUPS + main_flags.current_device - 1) * MEMORY_SUBPOINTS;	//points_group_ind * MEMORY_SUBPOINTS;

	pp_points_menu[beacons_group_start]->exist_flag = 0;			//clear sub-point 0
	for(uint8_t j = 1; j < MEMORY_SUBPOINTS; j++)
	{
		if(pp_points_menu[beacons_group_start + j]->exist_flag == 1)
		{
		pp_points_menu[beacons_group_start]->exist_flag++;			//save to sub-point 0
		}
	}

	pp_devices_menu[main_flags.current_device]->beacon_flag?
			sprintf(&string_buffer[row][0], "tBcn%d", main_flags.current_device): sprintf(&string_buffer[row][0], "Dev%d:", main_flags.current_device);	//if is beacon or device
	draw_str_by_rows(0, row*18, &string_buffer[row][0], &Font_11x18, YELLOW,BLACK);

	if(pp_devices_menu[main_flags.current_device]->beacon_traced)	// && p_settings_menu->timeout_threshold "ignore"
	{
		(pp_devices_menu[main_flags.current_device]->gps_speed)?
				sprintf(&string_buffer[row][5], "%2dkm/h", pp_devices_menu[main_flags.current_device]->gps_speed):
				sprintf(&string_buffer[row][5], "traced");		//"Trcd%2d", pp_devices_menu[main_flags.current_device]->beacon_traced);

		(pp_devices_menu[main_flags.current_device]->gps_speed)?
				draw_str_by_rows(60, row*18, &string_buffer[row][5], &Font_11x18, CYAN,BLACK):
				draw_str_by_rows(60, row*18, &string_buffer[row][5], &Font_11x18, GREEN,BLACK);
	}
	else if(pp_devices_menu[main_flags.current_device]->beacon_lost)
	{
//		sprintf(&string_buffer[row][5], "!LOST!");	&string_buffer[row][5]
		draw_str_by_rows(60, row*18, "!LOST!", &Font_11x18, RED,BLACK);
	}
	else if(pp_points_menu[beacons_group_start]->exist_flag)
	{
		if(!p_settings_menu->timeout_threshold	&& pp_devices_menu[main_flags.current_device]->valid_fix_flag)
		{
			draw_str_by_rows(60, row*18, "ignore", &Font_11x18, YELLOW,BLACK);		//traced but will be forgotten
		}
		else if(pp_devices_menu[main_flags.current_device]->index_in_flash == -1)
		{
			draw_str_by_rows(60, row*18, "tempor", &Font_11x18, YELLOW,BLACK);		// lost and will be forgotten
		}
		else	//(pp_devices_menu[main_flags.current_device]->index_in_flash != -1)
		{
			sprintf(&string_buffer[row][5], "%dsaved", pp_points_menu[beacons_group_start]->exist_flag);	//amount of saved sub-points);
			draw_str_by_rows(60, row*18, &string_buffer[row][5], &Font_11x18, CYAN,BLACK);
		}
	}
	else
	{
		sprintf(&string_buffer[row][5], "absent");
		draw_str_by_rows(60, row*18, &string_buffer[row][5], &Font_11x18, MAGENTA,BLACK);
	}

	if(is_north_ready())
	{
		//show azimuth and distance to remote
		if(pp_devices_menu[main_flags.current_device]->valid_fix_flag)
		{
//ext		azimuth_relative_deg = azimuth_deg_signed[main_flags.current_device] - heading_deg;
			azimuth_relative_deg = pp_devices_menu[main_flags.current_device]->azimuth_deg_signed - heading_deg;
		}
		else
		{
			azimuth_relative_deg = pp_points_menu[beacons_group_start + 1]->azimuth_deg_signed - heading_deg;
			sprintf(&string_buffer[3][0], "Distance:%5d m", ((uint16_t)pp_points_menu[main_flags.current_device]->distance & 0xFFFF));
			pp_devices_menu[main_flags.current_device]->distance = (pp_points_menu[beacons_group_start + 1]->distance);
//ext		distance[main_flags.current_device] = (pp_points_menu[beacons_group_start + 1]->distance);
		}

		if(azimuth_relative_deg > 180) azimuth_relative_deg -= 360;
		if(azimuth_relative_deg < -180) azimuth_relative_deg += 360;

//ext	sprintf(&string_buffer[++row][0], "%4d%%%5dm", azimuth_relative_deg, (uint16_t)distance[main_flags.current_device]);
		sprintf(&string_buffer[++row][0], "%4d%%%5dm", azimuth_relative_deg, (uint16_t)pp_devices_menu[main_flags.current_device]->distance);
		if(pp_devices_menu[main_flags.current_device]->valid_fix_flag) draw_str_by_rows(0, row*18, &string_buffer[row][0], &Font_11x18, YELLOW,BLACK);		//if remote fix valid (validFixFlag[dev])
		else draw_str_by_rows(0, row*18, &string_buffer[row][0], &Font_11x18, MAGENTA,BLACK);
		//draw magnet arrow
		(heading_rad < 0)? (north_rad = -heading_rad): (north_rad = 2*M_PI - heading_rad);
		draw_arrow(63, 97, 57, north_rad_old, 28, BLACK, BLACK);
		draw_arrow(63, 97, 57, north_rad, 28, CYANB, RED);
		north_rad_old = north_rad;

//ext	if(distance[main_flags.current_device] > range * range_scale[range_ind])
		if(pp_devices_menu[main_flags.current_device]->distance > range * range_scale[range_ind])
		{
			for(; range_ind < 6; range_ind++)
			{
//ext			if(distance[main_flags.current_device] < range * range_scale[range_ind]) break;
				if(pp_devices_menu[main_flags.current_device]->distance < range * range_scale[range_ind]) break;
			}
		}
//ext	else if(distance[main_flags.current_device] < range * range_scale[range_ind] / 2)
		else if(pp_devices_menu[main_flags.current_device]->distance < range * range_scale[range_ind] / 2)
		{
			for(; range_ind > 0; range_ind--)
			{
//ext			if(distance[main_flags.current_device] > range * range_scale[range_ind] / 2) break;
				if(pp_devices_menu[main_flags.current_device]->distance > range * range_scale[range_ind] / 2) break;
			}
		}
	}else
	{
		draw_str_by_rows(0, (row+=1)*18, "TURN AROUND", &Font_11x18, RED,BLACK);
		draw_arrow(63, 97, 57, north_rad_old, 28, BLACK, BLACK);
	}

	if(pp_devices_menu[main_flags.current_device]->batt_voltage < 32)		//<3.2V
	{
		sprintf(&string_buffer[++row][0], " LOW");		//< 3.2 volt
	} else sprintf(&string_buffer[++row][0], "%d.%dV", pp_devices_menu[main_flags.current_device]->batt_voltage/10, pp_devices_menu[main_flags.current_device]->batt_voltage%10);
	if(pp_devices_menu[main_flags.current_device]->valid_fix_flag) draw_str_by_rows(0, row*18, &string_buffer[row][0], &Font_7x9, CYAN,BLACK);
	else draw_str_by_rows(0, row*18, &string_buffer[row][0], &Font_7x9, MAGENTA,BLACK);

	sprintf(&string_buffer[row][12], "%4ddB", pp_devices_menu[main_flags.current_device]->rssi);
	if(pp_devices_menu[main_flags.current_device]->valid_fix_flag) draw_str_by_rows(85, row*18, &string_buffer[row][12], &Font_7x9, CYAN,BLACK);		//if remote fix valid (validFixFlag[dev])
	else draw_str_by_rows(85, row*18, &string_buffer[row][12], &Font_7x9, MAGENTA,BLACK);

	row = 13;
	sprintf(&string_buffer[row][0], "%d.%02dV", (pp_devices_menu[this_device]->batt_voltage+270)/100,
	   	    		 	 	 	 	 (pp_devices_menu[this_device]->batt_voltage+270)%100);
									//(GetBatteryLevel()+270)/100, (GetBatteryLevel()+270)%100);
	draw_str_by_rows(0, 7+row*11, &string_buffer[row][0], &Font_7x9, GREEN,BLACK);
	sprintf(&string_buffer[row][13], "%4dm", range * range_scale[range_ind]);
	draw_str_by_rows(92, 7+row*11, &string_buffer[row][13], &Font_7x9, WHITE,BLACK);

	draw_circle(63, 97, 60, WHITE);

	for(uint8_t i = 1; i < MEMORY_SUBPOINTS; i++)
	{
		if(pp_points_menu[beacons_group_start + i]->exist_flag == 1) {
			if(pp_devices_menu[this_device]->valid_fix_flag) calc_point_position(beacons_group_start + i); //host device valid GPS fix pDop and accuracy
		}
	}

	int8_t fix_valid = 0;
	if(pp_devices_menu[this_device]->valid_fix_flag)
	{
		for(uint8_t i = 1; i < MEMORY_SUBPOINTS; i++)			//draw saved device points
		{
			if(pp_points_menu[beacons_group_start + i]->exist_flag == 1)
			{
				scaled_dist = (uint16_t)(pp_points_menu[beacons_group_start + i]->distance)*2  / range_scale[range_ind];
				azimuth_relative_rad = pp_points_menu[beacons_group_start + i]->azimuth_rad - heading_rad;
				erase_position(63, 97, distance_old[i], azimuth_relative_rad_old[i], 7);
				if(scaled_dist > range * 2)
				{
					scaled_dist = range * 2;
					draw_trace(63, 97, scaled_dist, azimuth_relative_rad, (8 - i), RED);
				}else draw_trace(63, 97, scaled_dist, azimuth_relative_rad, (8 - i), CYAN);
				distance_old[i] = scaled_dist;
				azimuth_relative_rad_old[i] = azimuth_relative_rad;
			}//else if(i == this_device) draw_position(63, 97, 0, 0, 7, i, YELLOW);
		}

		if(pp_devices_menu[main_flags.current_device]->valid_fix_flag)		//draw current device points
		{									//if remote fix valid
			fix_valid = 1;
//ext		scaled_dist = ((int16_t)distance[main_flags.current_device] & 0x1FFF)*2  / range_scale[range_ind];
			scaled_dist = ((int16_t)pp_devices_menu[main_flags.current_device]->distance & 0x1FFF)*2  / range_scale[range_ind];
//ext		azimuth_relative_rad = azimuth_rad[main_flags.current_device] - heading_rad;
			azimuth_relative_rad = pp_devices_menu[main_flags.current_device]->azimuth_rad - heading_rad;
			erase_position(63, 97, distance_old[main_flags.current_device], azimuth_relative_rad_old[main_flags.current_device], 7);
			if(scaled_dist > range * 2)
			{
				scaled_dist = range * 2;
				draw_position(63, 97, scaled_dist, azimuth_relative_rad, 7, main_flags.current_device, RED);
			}else draw_position(63, 97, scaled_dist, azimuth_relative_rad, 7, main_flags.current_device, YELLOW);
			distance_old[main_flags.current_device] = scaled_dist;
			azimuth_relative_rad_old[main_flags.current_device] = azimuth_relative_rad;
		}
		else if((distance_old[main_flags.current_device] > 3) && fix_valid)
		{
			fix_valid = 0;
			erase_position(63, 97, distance_old[main_flags.current_device], azimuth_relative_rad_old[main_flags.current_device], 7);	//erase or change CYAN to MAGENTA
		}
	}

	draw_position(63, 97, 0, 0, 7, this_device, GREEN);		//draw this device position
}
//--------------------------------NAVIGATION MENU SET--------------------------------
void navigation_up(void) {
	if(range_ind == 6) {
		range_ind = 0;
	}else {
		range_ind++;
	}
}
void navigation_down(void) {
	if(range_ind == 0) {
		range_ind = 6;
	}else {
		range_ind--;
	}
}
void navigation_ok(void) {		//other points on loop
	current_menu = M_BEACONS;
}
void beacons_ok(void)
{
	if(main_flags.current_device == p_settings_menu->devices_on_air) main_flags.current_device = 1;
	else main_flags.current_device++;
}
void beacons_esc(void)
{
	if(pp_devices_menu[this_device]->valid_fix_flag && pp_devices_menu[this_device]->flwtrek_flag)
		main_flags.find_nearest_trekpoint_flag = 1;
	current_menu = M_NAVIGATION;
}
//--------------------------------NAVIGATION MENU END--------------------------------
//-----------------------------------------------------------------------------------
//--------------------------------LAPS MENU----------------------------
void draw_laps(void)
{
//	row = get_current_item();
//	draw_char(3, 10+line*19, *">", &Font_11x18, YELLOW,BLACK);
	int8_t line = 0;
	int8_t hour;
	hour = p_timeData->hour + p_settings_menu->time_zone_hour;
	if(hour > 23) hour = hour - 24;
	int8_t elapsedHour = main_flags.elapsed_sec/3600;
	int8_t elapsedMin = main_flags.elapsed_sec/60 - elapsedHour*60;
	int8_t elapsedSec = main_flags.elapsed_sec - elapsedHour*3600 - elapsedMin*60;
	uint32_t averagePace = (main_flags.elapsed_sec/pp_devices_menu[this_device]->distance < 3)?	//seconds/m *1000/60 < 50min/km
			(1000*main_flags.elapsed_sec/pp_devices_menu[this_device]->distance): 0;			//seconds/kilometer

	if(main_flags.rtc_enabled || main_flags.fix_valid)
	{
		draw_str_by_rows(0, 0, "TIME, LAPS & DIST.", &Font_7x9, CYAN,BLACK);
		sprintf(&string_buffer[line][0], "%02d:%02d:%02d", hour, p_timeData->minute, p_timeData->second);
		sprintf(&string_buffer[line][9], " TIME");
	}else
	{
		draw_str_by_rows(0, 0, "RTC IS NOT APPLIED", &Font_7x9, ORANGE,BLACK);
		sprintf(&string_buffer[line][0], " ");
		sprintf(&string_buffer[line][9], "  TIME UNDEFINED");
	}

//	sprintf(&string_buffer[line][0], "%02d:%02d:%02d", hour, p_timeData->minute, p_timeData->second);
//	sprintf(&string_buffer[line][9], " TIME");
	line++;
	sprintf(&string_buffer[line][0], " ");//   %02d:%02d:%02d", startHour, startMinute, startSecond);
	sprintf(&string_buffer[line][9], "GNSS fix %02d:%02d:%02d", startHour, startMinute, startSecond);
	line++;
	sprintf(&string_buffer[line][0], " %01d:%02d:%02d", elapsedHour, elapsedMin, elapsedSec);
	sprintf(&string_buffer[line][9], "ELAPSED");
	line++;
	sprintf(&string_buffer[line][0], " %2ldk%03ldm", pp_devices_menu[this_device]->distance/1000,
			pp_devices_menu[this_device]->distance%1000);
	sprintf(&string_buffer[line][9], " DIST");
	line++;
	sprintf(&string_buffer[line][0], "%2ld:%02ldm/k", averagePace/60, averagePace%60);
//	sprintf(&string_buffer[line][0], "    %3dkm/h", pp_devices_menu[this_device]->gps_speed);
	sprintf(&string_buffer[line][9], "AVRGE");
	line++;
	for (uint8_t k = 0; k < line; k++)
	{
		if(k%2)
		{
			draw_str_by_rows(40, 10+k*19, &string_buffer[k][0], &Font_11x18, GREEN,BLACK);
			draw_str_by_rows(4, 16+k*19, &string_buffer[k][9], &Font_7x9, GREEN,BLACK);
//			draw_str_by_rows(0, 10+k*19, &string_buffer[k][12], &Font_11x18, DARKGREEN,BLACK);
		}
		else
		{
			draw_str_by_rows(40, 10+k*19, &string_buffer[k][0], &Font_11x18, LIGHTGREY,BLACK);
			draw_str_by_rows(0, 16+k*19, &string_buffer[k][9], &Font_7x9, LIGHTGREY,BLACK);
//			draw_str_by_rows(0, 10+k*19, &string_buffer[k][12], &Font_11x18, DARKGREY,BLACK);
		}
	}
//	draw_str_by_rows(2, 16+(line-1)*19, "AVRG", &Font_7x9, LIGHTGREY,BLACK);

	if(lapsSaved)
	{
		sprintf(&string_buffer[line][0], " %2d:%02d/%3dm", lapsTimeSaved/60, lapsTimeSaved%60, lapsDistSaved);
		draw_str_by_rows(3, 10+line*19, &string_buffer[line][0], &Font_11x18, DARKCYAN,BLACK);
		sprintf(&string_buffer[line][0], "%d", lapsCounter);
		draw_str_by_rows(1, 10+line*19, &string_buffer[line][0], &Font_11x18, YELLOW,BLACK);
		line++;
		sprintf(&string_buffer[line][0], " %2d:%02d/%3dm", main_flags.lapsTime/60, main_flags.lapsTime%60, main_flags.lapsDist);
		main_flags.laps_afoot? draw_str_by_rows(3, 10+line*19, &string_buffer[line][0], &Font_11x18, CYAN,BLACK):
							draw_str_by_rows(3, 10+line*19, &string_buffer[line][0], &Font_11x18, DARKCYAN,BLACK);
		draw_char(3, 10+line*19, *">", &Font_11x18, YELLOW,BLACK);		//+5 due to 2 digit lapsCounter
	}
	else
	{
		if(lapsCounter > 1)
		{
			sprintf(&string_buffer[line][0], " %2d:%02d/%3dm", lapsTimeSaved/60, lapsTimeSaved%60, lapsDistSaved);
			draw_str_by_rows(3, 10+line*19, &string_buffer[line][0], &Font_11x18, DARKCYAN,BLACK);
			sprintf(&string_buffer[line][0], "%d", lapsCounter - 1);
			draw_str_by_rows(1, 10+line*19, &string_buffer[line][0], &Font_11x18, YELLOW,BLACK);
			line++;
			sprintf(&string_buffer[line][0], " %2d:%02d/%3dm", main_flags.lapsTime/60, main_flags.lapsTime%60, main_flags.lapsDist);
			draw_str_by_rows(3, 10+line*19, &string_buffer[line][0], &Font_11x18, CYAN,BLACK);
			sprintf(&string_buffer[line][0], "%d", lapsCounter);
			draw_str_by_rows(1, 10+line*19, &string_buffer[line][0], &Font_11x18, YELLOW,BLACK);
		}
		else
		{
			sprintf(&string_buffer[line][0], " %2d:%02d/%3dm", main_flags.lapsTime/60, main_flags.lapsTime%60, main_flags.lapsDist);
			draw_str_by_rows(3, 10+line*19, &string_buffer[line][0], &Font_11x18, CYAN,BLACK);
			sprintf(&string_buffer[line][0], "%d", lapsCounter);
			draw_str_by_rows(1, 10+line*19, &string_buffer[line][0], &Font_11x18, YELLOW,BLACK);
			line++;
			sprintf(&string_buffer[line][0], "-----------");
			draw_str_by_rows(3, 10+line*19, &string_buffer[line][0], &Font_11x18, DARKGREEN,BLACK);
		}
	}
	line++;
	sprintf(&string_buffer[line][0], "   %2ld:%02ldm/k", pp_devices_menu[this_device]->gps_pace/60,
			pp_devices_menu[this_device]->gps_pace%60);
//	sprintf(&string_buffer[line][12], "Pace");
	draw_str_by_rows(3, 10+line*19, &string_buffer[line][0], &Font_11x18, GREENYELLOW,BLACK);
	draw_str_by_rows(2, 16+line*19, "PACE", &Font_7x9, GREEN,BLACK);
//	sprintf(&string_buffer[5][0], "%d", main_flags.laps_counter);
//	draw_str_by_rows(3, 10+5*19, &string_buffer[5][0], &Font_11x18, YELLOW,BLACK);
}
void new_laps(void)
{
	main_flags.laps_afoot? (lapsTimeSaved = main_flags.lapsTime-1): (lapsTimeSaved = main_flags.lapsTime);
	main_flags.laps_afoot = 1;
	lapsDistSaved = main_flags.lapsDist;
	main_flags.lapsDist = p_settings_menu->lap_path = 0;
	lapsSaved = 0;
	main_flags.lapsTime = 1;					//1 due to menu delay
	(lapsCounter < 99)? lapsCounter++: (lapsCounter = 1);
}
void continue_laps(void)
{
	if(lapsSaved)
	{
		if(main_flags.laps_afoot)
		{
			main_flags.laps_afoot = 0;
			main_flags.lapsTime--;
		}
		else
		{
			lapsSaved = 0;
			main_flags.lapsTime = 0;
			main_flags.lapsDist = 0;
			lapsCounter = 0;
		}
	}
	else if(main_flags.laps_afoot)
	{
		lapsSaved = 1;
		lapsTimeSaved = main_flags.lapsTime-1;	//-1 if main_flags.pps_synced
		lapsDistSaved = main_flags.lapsDist;
	}
}
//--------------------------------LAPS MENU END--------------------------------
//-----------------------------------------------------------------------------------
//--------------------------------DEVICES MENU----------------------------
void draw_this_device(void)
{
	uint8_t day = PVTbuffer[7+6];
	uint8_t month = PVTbuffer[6+6];
	uint16_t year = (PVTbuffer[5+6]<<8) + PVTbuffer[4+6];
	uint8_t hour = PVTbuffer[14];
	row = 0;

	if(pp_devices_menu[this_device]->valid_date_flag)	//bit 5: information about UTC Date and Time of Day validity conﬁrmation is available
	{
		year = year - 2000;
		hour = hour + p_settings_menu->time_zone_hour;
		if(hour > 23) hour = hour - 24;
	}else day = month = year = hour = 0;

		sprintf(&string_buffer[0][0], " Device: %d ", this_device);
			if(pp_devices_menu[this_device]->valid_fix_flag) draw_str_by_rows(0, 0, &string_buffer[0][0], &Font_11x18, GREENYELLOW,BLACK);		//if fix valid
			else draw_str_by_rows(0, 0, &string_buffer[0][0], &Font_11x18, MAGENTA,BLACK);

		sprintf(&string_buffer[2][0], "%2d %3d.%03dMHz SF%02d", p_settings_menu->freq_channel,
				(433000 + 50 + p_settings_menu->freq_channel * 25)/1000, (433000 + 50 + p_settings_menu->freq_channel * 25)%1000,
												      p_settings_menu->spreading_factor);
		sprintf(&string_buffer[3][0], "TxPWR %2ddBm CR=4/%d", p_tx_power_values[p_settings_menu->tx_power_opt], p_coding_rate_values[p_settings_menu->coding_rate_opt]);
		sprintf(&string_buffer[4][0], "CPU: %02d%%C %d.%02dVolt",pp_devices_menu[this_device]->core_temperature,
													 (pp_devices_menu[this_device]->core_voltage+270)/100,
				  	  	  	  	  	  	  	  	  	 (pp_devices_menu[this_device]->core_voltage+270)%100);
		sprintf(&string_buffer[5][0], "Battery:  %d.%02dVolt", (pp_devices_menu[this_device]->batt_voltage+270)/100,
 	  	  	  	  	  	  	  	   	   	   	   	    (pp_devices_menu[this_device]->batt_voltage+270)%100);
		sprintf(&string_buffer[6][0], "0x%lX Flag%02X%02d",
						main_flags.settings_address, p_settings_menu->settings_init_flag, main_flags.settings_index);
		sprintf(&string_buffer[7][0], "ADC calibration%3d", main_flags.adc_calibration_factor);

		for (uint8_t k = 2; k < 8; k++)
		{
			draw_str_by_rows(0, k*11-3, &string_buffer[k][0], &Font_7x9, YELLOW,BLACK);
		}

		sprintf(&string_buffer[8][0], " %5s pDop:%2d.%02d ", fixType[pp_devices_menu[main_flags.current_device]->fix_type_opt],
				pp_devices_menu[main_flags.current_device]->p_dop/100, pp_devices_menu[main_flags.current_device]->p_dop%100);

		sprintf(&string_buffer[9][0], "%02d/%02d/%02d  %02d:%02d:%02d", day, month, year, hour, PVTbuffer[15], PVTbuffer[16]);
//show first byte		sprintf(&string_buffer[9][0], "0x%X : %ld", pp_devices_menu[this_device]->latitude.as_array[3], pp_devices_menu[this_device]->latitude.as_integer);
		sprintf(&string_buffer[10][0], "Latit : %ld", pp_devices_menu[this_device]->latitude.as_integer);	//((int32_t)(PVTbuffer[37]<<24)+(PVTbuffer[36]<<16)+(PVTbuffer[35]<<8)+PVTbuffer[34]));
//show first byte		sprintf(&string_buffer[10][0], "0x%X : %ld", pp_devices_menu[this_device]->longitude.as_array[3], pp_devices_menu[this_device]->longitude.as_integer);
		sprintf(&string_buffer[11][0], "Longit: %ld", pp_devices_menu[this_device]->longitude.as_integer);	//((int32_t)(PVTbuffer[33]<<24)+(PVTbuffer[32]<<16)+(PVTbuffer[31]<<8)+PVTbuffer[30]));
		sprintf(&string_buffer[12][0], "HeightMSL:  %4dm", ((PVTbuffer[39+6]<<24)+(PVTbuffer[38+6]<<16)+(PVTbuffer[37+6]<<8)+PVTbuffer[36+6])/1000);
		sprintf(&string_buffer[13][0], "GNSSspeed:%3dkm/h", pp_devices_menu[this_device]->gps_speed);

		(pp_devices_menu[this_device]->gps_speed > GPS_SPEED_THRS)?
				sprintf(&string_buffer[14][0], "HeadingGNSS: %4d%%", pp_devices_menu[this_device]->gps_heading):
				sprintf(&string_buffer[14][0], "HeadingMagn: %4d%%", heading_deg);

		for (uint8_t k = 8; k < 15; k++)
		{
			(pp_devices_menu[main_flags.current_device]->valid_fix_flag)?
					draw_str_by_rows(0, k*11-3, &string_buffer[k][0], &Font_7x9, GREEN,BLACK):
					draw_str_by_rows(0, k*11-3, &string_buffer[k][0], &Font_7x9, MAGENTA,BLACK);
		}
}

void draw_devices(void)
{
	current_menu = M_DEVICES;

	if(main_flags.current_device == this_device) draw_this_device();
	else
	{
		if(pp_devices_menu[main_flags.current_device]->device_received == main_flags.current_device)		//data has received
		{
			if(pp_devices_menu[main_flags.current_device]->beacon_flag)		//(buffer[0] >> 7)		//if is beacon
			{
				sprintf(&string_buffer[0][0], "tBcn%d data:", pp_devices_menu[main_flags.current_device]->device_received);			//(buffer[0] & 0x03));
			}
			else sprintf(&string_buffer[0][0], " Dev%d data:", pp_devices_menu[main_flags.current_device]->device_received);		//(buffer[0] & 0x03));
		}
		else sprintf(&string_buffer[0][0], " NoDevice %d", main_flags.current_device);

		draw_str_by_rows(0, 0, &string_buffer[0][0], &Font_11x18, GREENYELLOW,BLACK);

		//fixType only 2 bits used to transmit, pDop/10 (0...25.5)	buffer[15]/10, buffer[15]%10);
		sprintf(&string_buffer[2][0], " %5s pDop:%2d.%d", fixType[pp_devices_menu[main_flags.current_device]->fix_type_opt],
				pp_devices_menu[main_flags.current_device]->p_dop/10, pp_devices_menu[main_flags.current_device]->p_dop%10);

//	sprintf(&string_buffer[3][0], "Date../09 %02d:%02d:%02d", pp_devices_menu[main_flags.current_device]->time_hours,
//			pp_devices_menu[main_flags.current_device]->time_minutes, pp_devices_menu[main_flags.current_device]->time_seconds);

//ext	sprintf(&string_buffer[3][0], "Distance:%5d m", ((uint16_t)distance[main_flags.current_device] & 0xFFFF));
		sprintf(&string_buffer[3][0], "Distance:%5d m", ((uint16_t)pp_devices_menu[main_flags.current_device]->distance & 0xFFFF));
//ext	azimuth_relative_deg = azimuth_deg_signed[main_flags.current_device] - heading_deg;
		azimuth_relative_deg = pp_devices_menu[main_flags.current_device]->azimuth_deg_signed - heading_deg;
		if(azimuth_relative_deg > 180) azimuth_relative_deg -= 360;
		if(azimuth_relative_deg < -180) azimuth_relative_deg += 360;
		sprintf(&string_buffer[4][0], "AzRelative: %03d%%", azimuth_relative_deg);

		sprintf(&string_buffer[5][0], "Speed:   %3d km/h", pp_devices_menu[main_flags.current_device]->gps_speed);
		if(pp_devices_menu[main_flags.current_device]->gps_speed)
		{
			sprintf(&string_buffer[6][0], "HeadingGPS:  %03d%% ", pp_devices_menu[main_flags.current_device]->gps_heading);
		}else 	sprintf(&string_buffer[6][0], "Device%d not moving", main_flags.current_device);

//	sprintf(&string_buffer[6][0], "Azimuth_s : %03d%%", azimuth_deg_signed[main_flags.current_device]);
//	sprintf(&string_buffer[7][0], "Azimuth_u : %03d%%", azimuth_deg_unsigned[main_flags.current_device]);
		sprintf(&string_buffer[7][0], "                  ");

		if(pp_devices_menu[main_flags.current_device]->batt_voltage < 32)
		{
			sprintf(&string_buffer[8][0], "Battery :  low    ");		//<=3.2 volt
		} else sprintf(&string_buffer[8][0], "Battery: %d.%d Volt ", pp_devices_menu[main_flags.current_device]->batt_voltage/10, pp_devices_menu[main_flags.current_device]->batt_voltage%10);

		sprintf(&string_buffer[9][0], "RSSI: %ddBm", pp_devices_menu[main_flags.current_device]->rssi);
		sprintf(&string_buffer[10][0], " SNR: %02ddB", pp_devices_menu[main_flags.current_device]->snr);

		(p_settings_menu->spreading_factor == 12)? sprintf(&string_buffer[11][0], "RX%d to TX%d: %4dmS",
pp_devices_menu[main_flags.current_device]->device_received,(this_device - pp_devices_menu[main_flags.current_device]->device_received), main_flags.endRX_2_TX):
		sprintf(&string_buffer[11][0], "RX%d to TX%d: %4dmS", pp_devices_menu[main_flags.current_device]->device_received, this_device, main_flags.endRX_2_TX);

		sprintf(&string_buffer[12][0], "Latit : %ld", pp_devices_menu[main_flags.current_device]->latitude.as_integer);
		sprintf(&string_buffer[13][0], "Longit: %ld", pp_devices_menu[main_flags.current_device]->longitude.as_integer);

		for (uint8_t k = 2; k < 14; k++)
		{
			(pp_devices_menu[main_flags.current_device]->valid_fix_flag)?
					(draw_str_by_rows(0, 4+k*11, &string_buffer[k][0], &Font_7x9, GREEN,BLACK)):
					(draw_str_by_rows(0, 4+k*11, &string_buffer[k][0], &Font_7x9, MAGENTA,BLACK));
		}
	}// end of else (main_flags.current_device != this_device)
}
//-----------------------------DEVICES MENU SET------------------------------------
void scroll_devices_up(void) {
        if (main_flags.current_device == p_settings_menu->devices_on_air)
        {
        	main_flags.current_device = 1;
        }else {
        	main_flags.current_device++;
        }
        draw_devices();
}
void scroll_devices_down(void) {
        if (main_flags.current_device == 1)
        {
        	main_flags.current_device = p_settings_menu->devices_on_air;
        }else {
        	main_flags.current_device--;
        }
        draw_devices();
}
void devices_ok(void) {
	current_menu = M_DEVICE_SUBMENU;
}
void devices_esc(void) {
	current_menu = M_MAIN;
}
//---------------------------------DEVICES MENU END---------------------------------
//---------------------------------------------------------------------------
//-----------------------------MEMORY POINTS MENU----------------------------
void draw_device_submenu(void)
{
	for(uint8_t i = 0; i < MEMORY_POINT_GROUPS; i++)							//calculate saved memory points
	{
		pp_points_menu[i * MEMORY_SUBPOINTS]->exist_flag = 0;			//clear sub-point 0
		for(uint8_t j = 1; j < MEMORY_SUBPOINTS; j++)
		{
			if(pp_points_menu[i * MEMORY_SUBPOINTS + j]->exist_flag == 1) {
				pp_points_menu[i * MEMORY_SUBPOINTS]->exist_flag++;	//save to sub-point 0: 0, 28, 55, 83, 111, ...
			}
		}
	}

	if(pp_devices_menu[main_flags.current_device]->valid_fix_flag)		//if fix valid for this or current remote device
	{
		sprintf(&string_buffer[0][0], " Save %d as:", main_flags.current_device);
		draw_str_by_rows(0, 0, &string_buffer[0][0], &Font_11x18, CYAN,BLACK);

		row = get_current_item();
		for (uint8_t k = 0; k < MEMORY_POINT_GROUPS; k++)		//draw points groups
		{
			sprintf(&string_buffer[k][0], " %4s   /%1d", get_points_group_short(k), pp_points_menu[k * MEMORY_SUBPOINTS]->exist_flag);	//amount of saved sub-points
			if(k == row) draw_str_by_rows(3, 24+k*18, &string_buffer[k][0], &Font_11x18, YELLOW,BLACK);		//active points group
			else draw_str_by_rows(3, 24+k*18, &string_buffer[k][0], &Font_11x18, GREEN,BLACK);				//other points groups
		}
		draw_char(3, 24+row*18, *">", &Font_11x18, YELLOW,BLACK);

	}else {
		draw_str_by_rows(0, 54, "  NOTHING ", &Font_11x18, CYAN,BLACK);
		draw_str_by_rows(0, 81, "  TO SAVE", &Font_11x18, CYAN,BLACK);
		HAL_Delay(300);
		shortBeeps(3);
		fill_screen(BLACK);
		current_menu = M_DEVICES;
	}
}
void draw_set_points(void)
{
	sprintf(&string_buffer[0][0], " Save %d as:", main_flags.current_device);
	draw_str_by_rows(0, 0, &string_buffer[0][0], &Font_11x18, CYAN,BLACK);

	main_flags.current_point_group = row;
	for (uint8_t k = 0; k < MEMORY_POINT_GROUPS; k++)
	{
		sprintf(&string_buffer[k][0], " %4s  %1d/%1d", get_points_group_short(k), memory_subpoint_ind[k], pp_points_menu[k * MEMORY_SUBPOINTS]->exist_flag);
		if(k == row)
		{
			draw_str_by_rows(3, 24+k*18, &string_buffer[k][0], &Font_11x18, CYAN,BLACK);									//active points group
			if(pp_points_menu[main_flags.current_point_group * MEMORY_SUBPOINTS + memory_subpoint_ind[k]]->exist_flag == 1)
			{
				draw_str_by_rows(3, 24+k*18, &string_buffer[k][0], &Font_11x18, RED,BLACK);									//if sub-point already exist
			}
		}else draw_str_by_rows(3, 24+k*18, &string_buffer[k][0], &Font_11x18, GREEN,BLACK);									//other points groups
	}
	draw_char(3, 24+row*18, *">", &Font_11x18, CYAN,BLACK);
}
//-------------------------MEMORY POINTS SET----------------------------
void set_subpoint_up(void) {
	if(memory_subpoint_ind[main_flags.current_point_group] == MEMORY_SUBPOINTS - 1)	//if (memory_subpoint == MEMORY_SUBPOINTS)
    {
		memory_subpoint_ind[main_flags.current_point_group] = 1;
    }else {
    	memory_subpoint_ind[main_flags.current_point_group]++;
    }
}
void set_subpoint_down(void) {
    if (memory_subpoint_ind[main_flags.current_point_group] < 2)
    {
    	memory_subpoint_ind[main_flags.current_point_group] = MEMORY_SUBPOINTS - 1;
    }else {
    	memory_subpoint_ind[main_flags.current_point_group]--;
    }
}
void set_subpoint_ok(void) {
    if (memory_subpoint_ind[main_flags.current_point_group]) {    //if (!= 0) copy current device/point to selected mem point

   	pp_points_menu[main_flags.current_point_group * MEMORY_SUBPOINTS + memory_subpoint_ind[main_flags.current_point_group]]->exist_flag = 1;
   	pp_points_menu[main_flags.current_point_group * MEMORY_SUBPOINTS + memory_subpoint_ind[main_flags.current_point_group]]->latitude.as_integer =
   			pp_devices_menu[main_flags.current_device]->latitude.as_integer;
   	pp_points_menu[main_flags.current_point_group * MEMORY_SUBPOINTS + memory_subpoint_ind[main_flags.current_point_group]]->longitude.as_integer =
   			pp_devices_menu[main_flags.current_device]->longitude.as_integer;
/* postpone save to flash when manual power off */
   	flag_group_has_changed[main_flags.current_point_group] = 1;
   	pp_points_menu[main_flags.current_point_group * MEMORY_SUBPOINTS]->exist_flag = 0;	//clear subpoint 0
   	memory_subpoint_ind[main_flags.current_point_group] = 0;
//  points_group_save(main_flags.current_point_group);				//save to flash now

    current_menu = M_DEVICE_SUBMENU;
	}else current_menu = M_SET_POINTS;
}

void save_start_pos(void) {
	main_flags.elapsed_sec = 0;
	startHour = p_timeData->hour + p_settings_menu->time_zone_hour;
	if(startHour > 23) startHour = startHour - 24;
	startMinute = p_timeData->minute;
	startSecond = p_timeData->second;

 	fill_screen(BLACK);

	memory_subpoint_ind[START_POS_GROUP] = 1;
/* check if saved memory points already exist and return first free position */
	for(int8_t i = 1; i < MEMORY_SUBPOINTS; i++)
	{
		if(pp_points_menu[START_POS_GROUP * MEMORY_SUBPOINTS + memory_subpoint_ind[START_POS_GROUP]]->exist_flag == 1)
		{
			if(memory_subpoint_ind[START_POS_GROUP] == MEMORY_SUBPOINTS - 1)
		    {
//				memory_subpoint_ind[main_flags.current_point_group] = 1;
				break;
		    }else {
		    	memory_subpoint_ind[START_POS_GROUP]++;
		    }
		}
		else break;
	}

	firstFreeStartPoint = memory_subpoint_ind[START_POS_GROUP];
/* set the same current item for menu Points */
	item_table[2].cur_item = START_POS_GROUP;
/* set group for Nav2Points menu*/
	points_group_ind = START_POS_GROUP;

	previous_menu = current_menu;
	current_menu = M_CONFIRM_SAVEGROUP;
}
void draw_save_group(void)
{
	main_flags.current_point_group = START_POS_GROUP;	//restore if lcd_off

	draw_str_by_rows(8, 7, "SAVE START", &Font_11x18, CYAN,BLACK);

	sprintf(&string_buffer[0][0], "AS POINT<%d>", memory_subpoint_ind[START_POS_GROUP]);
	if(pp_points_menu[START_POS_GROUP * MEMORY_SUBPOINTS + memory_subpoint_ind[START_POS_GROUP]]->exist_flag == 1)
	{
		draw_str_by_rows(3, 1*19+7, &string_buffer[0][0], &Font_11x18, ORANGE,BLACK);		//if sub-point already exist
	}
	else draw_str_by_rows(3, 1*19+7, &string_buffer[0][0], &Font_11x18, YELLOW,BLACK);		//active points group

	draw_str_by_rows(14, 2*19+7, "TO FLASH?", &Font_11x18, CYAN,BLACK);
	draw_str_by_rows(5, 3*19+7, "    OK", &Font_11x18, YELLOW,BLACK);
	draw_str_by_rows(5, 4*19+7, "    or", &Font_11x18, CYAN,BLACK);
	sprintf(&string_buffer[1][0], "LEFT AS %d", firstFreeStartPoint);
	draw_str_by_rows(14, 5*19+7, &string_buffer[1][0], &Font_11x18, GREEN,BLACK);
	draw_str_by_rows(8, 6*19+7, "IN THE RAM", &Font_11x18, CYAN,BLACK);
	draw_str_by_rows(0, 7*19+7, "    ESC", &Font_11x18, GREEN,BLACK);
}
void confirm_save_group(void)
{
   	pp_points_menu[main_flags.current_point_group * MEMORY_SUBPOINTS + memory_subpoint_ind[main_flags.current_point_group]]->exist_flag = 1;
   	pp_points_menu[main_flags.current_point_group * MEMORY_SUBPOINTS + memory_subpoint_ind[main_flags.current_point_group]]->latitude.as_integer =
   			pp_devices_menu[main_flags.current_device]->latitude.as_integer;
   	pp_points_menu[main_flags.current_point_group * MEMORY_SUBPOINTS + memory_subpoint_ind[main_flags.current_point_group]]->longitude.as_integer =
   			pp_devices_menu[main_flags.current_device]->longitude.as_integer;
/* erase points higher-numbered memory_subpoint_ind[main_flags.current_point_group] */
	for(int8_t i = 1+memory_subpoint_ind[main_flags.current_point_group]; i < MEMORY_SUBPOINTS; i++)
	{
		pp_points_menu[main_flags.current_point_group * MEMORY_SUBPOINTS + i]->exist_flag = 0;
	}
/* save to flash now */
   	points_group_save(main_flags.current_point_group);
//  saved_group_load(main_flags.current_point_group);
	current_menu = M_NAVTO_POINTS;
}
void decline_save_group(void)
{
	memory_subpoint_ind[main_flags.current_point_group] = firstFreeStartPoint;

	pp_points_menu[main_flags.current_point_group * MEMORY_SUBPOINTS + memory_subpoint_ind[main_flags.current_point_group]]->exist_flag = 1;
	pp_points_menu[main_flags.current_point_group * MEMORY_SUBPOINTS + memory_subpoint_ind[main_flags.current_point_group]]->latitude.as_integer =
			pp_devices_menu[main_flags.current_device]->latitude.as_integer;
	pp_points_menu[main_flags.current_point_group * MEMORY_SUBPOINTS + memory_subpoint_ind[main_flags.current_point_group]]->longitude.as_integer =
			pp_devices_menu[main_flags.current_device]->longitude.as_integer;

	current_menu = previous_menu;
}
void set_subpoint_esc(void) {
	pp_points_menu[main_flags.current_point_group * MEMORY_SUBPOINTS]->exist_flag = 0;			//clear subpoint 0
	memory_subpoint_ind[main_flags.current_point_group] = 0;   //exit no save, reset value
//	saved_group_load(main_flags.current_point_group);
//	memory_points_load();
    current_menu = M_DEVICE_SUBMENU;
}
//---------------------------------DEVICES MENU END---------------------------------
//----------------------------------------------------------------------
//--------------------------------NAV TO POINTS MENU--------------------------------
void draw_navto_points(void)
{
	row = 0;
//	int8_t ind = 0;		//out of the function to roll up points in group menu
	uint8_t sub_point_ind = 0;
	uint8_t sub_point[] = {0, 0, 0, 0, 0, 0, 0};		//1...7
	uint8_t points_group_start = points_group_ind * MEMORY_SUBPOINTS;

		for(uint8_t i = 1; i < MEMORY_SUBPOINTS; i++)
		{
			if(pp_points_menu[points_group_start + i]->exist_flag == 1) {
				if(pp_devices_menu[this_device]->valid_fix_flag) calc_point_position(points_group_start + i); //host device valid GPS fix pDop and accuracy
				sub_point[sub_point_ind] = i;						//save number of saved sub-point
//				if(sub_point_ind++ > 9) i = MEMORY_SUBPOINTS;			//restrict to 9 for a while
				sub_point_ind++;	//amount of saved sub points
			}
		}

	if(sub_point[ind]) {
		azimuth_relative_deg = pp_points_menu[points_group_start+sub_point[ind]]->azimuth_deg_signed - heading_deg;
		if(azimuth_relative_deg > 180) azimuth_relative_deg -= 360;
		if(azimuth_relative_deg < -180) azimuth_relative_deg += 360;
	}else azimuth_relative_deg = 0;
	sprintf(&string_buffer[0][0], "%1d:%5dm%3d%%", sub_point[ind], (uint16_t)(pp_points_menu[points_group_start+sub_point[ind]]->distance), azimuth_relative_deg);
	ind++;
	if(sub_point[ind]) {
		azimuth_relative_deg = pp_points_menu[points_group_start+sub_point[ind]]->azimuth_deg_signed - heading_deg;
		if(azimuth_relative_deg > 180) azimuth_relative_deg -= 360;
		if(azimuth_relative_deg < -180) azimuth_relative_deg += 360;
	}else azimuth_relative_deg = 0;
	sprintf(&string_buffer[1][0], "%1d:%5dm%3d%%", sub_point[ind], (uint16_t)(pp_points_menu[points_group_start+sub_point[ind]]->distance), azimuth_relative_deg);
	ind++;
	if(sub_point[ind]) {
		azimuth_relative_deg = pp_points_menu[points_group_start+sub_point[ind]]->azimuth_deg_signed - heading_deg;
		if(azimuth_relative_deg > 180) azimuth_relative_deg -= 360;
		if(azimuth_relative_deg < -180) azimuth_relative_deg += 360;
	}else azimuth_relative_deg = 0;
	sprintf(&string_buffer[2][0], "%1d:%5dm%3d%%", sub_point[ind], (uint16_t)(pp_points_menu[points_group_start+sub_point[ind]]->distance), azimuth_relative_deg);
	((ind + 2) > sub_point_ind)? ind = 0: ind--;
//	sprintf(&string_buffer[3][0], "%4s:%d", get_points_group_short(points_group_ind), sub_point_ind);
	sprintf(&string_buffer[3][0], "%4s", get_points_group_short(points_group_ind));
	for (row = 0; row < 3; row++)
	{
		draw_str_by_rows(0, row*12, &string_buffer[row][0], &Font_7x9, GREEN,BLACK);
	}
	draw_str_by_rows(3, 3*12, &string_buffer[3][0], &Font_7x9, CYAN,BLACK);

	row = 0;
	if(pp_devices_menu[this_device]->gps_speed > GPS_SPEED_THRS)
	{
		sprintf(&string_buffer[row][8], "%2d/h", pp_devices_menu[this_device]->gps_speed);
		draw_str_by_rows(83, row*19, &string_buffer[row][8], &Font_11x18, GREEN,BLACK);
		(heading_deg > -99)? (sprintf(&string_buffer[row+=1][8], "%3d%%", heading_deg)): (sprintf(&string_buffer[row+=1][8], "%3d", heading_deg));
		draw_str_by_rows(83, (row)*19, &string_buffer[row][8], &Font_11x18, YELLOW,BLACK);
	}else if(is_north_ready())
	{
//		sprintf(&string_buffer[row][8], "Magn");		//"Axis%3d ", (p_settings_menu->accel_max.as_integer - p_acceleration_menu->acc_z.as_integer));
		draw_str_by_rows(83, row*19, "Magn", &Font_11x18, CYANB,BLACK);
		(heading_deg > -99)? (sprintf(&string_buffer[row+=1][8], "%3d%%", heading_deg)): (sprintf(&string_buffer[row+=1][8], "%3d", heading_deg));
		draw_str_by_rows(83, row*19, &string_buffer[row][8], &Font_11x18, GREEN,BLACK);
	}else
	{
//		sprintf(&string_buffer[row][8], "TURN");
		draw_str_by_rows(83, row*19, "TURN", &Font_11x18, RED,BLACK);
//		sprintf(&string_buffer[row+=1][8], "ARND");
		draw_str_by_rows(83, (++row)*19, "ARND", &Font_11x18, RED,BLACK);
	}

	if(is_north_ready())
	{
		(heading_rad < 0)? (north_rad = -heading_rad): (north_rad = 2*M_PI - heading_rad);
		draw_arrow(63, 97, 57, north_rad_old, 28, BLACK, BLACK);
		draw_arrow(63, 97, 57, north_rad, 28, CYANB, RED);
		north_rad_old = north_rad;
	}else draw_arrow(63, 97, 57, north_rad_old, 28, BLACK, BLACK);

	row = 13;
	sprintf(&string_buffer[row][0], "%d.%02dV", (pp_devices_menu[this_device]->batt_voltage+270)/100,
  	   	    		 	 	 	 	 (pp_devices_menu[this_device]->batt_voltage+270)%100);
										//(GetBatteryLevel()+270)/100, (GetBatteryLevel()+270)%100);
	draw_str_by_rows(0, 7+row*11, &string_buffer[row][0], &Font_7x9, GREEN,BLACK);
	sprintf(&string_buffer[row][13], "%4dm", range * range_scale[range_ind]);
	draw_str_by_rows(92, 7+row*11, &string_buffer[row][13], &Font_7x9, WHITE,BLACK);

	draw_circle(63, 97, 60, WHITE);

	for(uint8_t i = 1; i < MEMORY_SUBPOINTS; i++)
	{
		if(pp_points_menu[points_group_start + i]->exist_flag == 1) {
			scaled_dist = ((uint16_t)(pp_points_menu[points_group_start + i]->distance & 0x1FFF))*2  / range_scale[range_ind];
			azimuth_relative_rad = pp_points_menu[points_group_start + i]->azimuth_rad - heading_rad;
			erase_position(63, 97, distance_old[i], azimuth_relative_rad_old[i], 7);
			if(scaled_dist > range * 2)
			{
				scaled_dist = range * 2;
				draw_position(63, 97, scaled_dist, azimuth_relative_rad, 7, i, RED);
			}else draw_position(63, 97, scaled_dist, azimuth_relative_rad, 7, i, YELLOW);
			distance_old[i] = scaled_dist;
			azimuth_relative_rad_old[i] = azimuth_relative_rad;
		}//else if(i == this_device) draw_position(63, 97, 0, 0, 7, i, YELLOW);
	}
	draw_position(63, 97, 0, 0, 7, this_device, GREEN);
}
//------------------------------NAV TO POINTS MENU SET----------------------------
void navto_points_ok(void) {		//other points on loop
	if (points_group_ind == (MEMORY_POINT_GROUPS - 1)) points_group_ind = 0;
    else points_group_ind++;
/* set the same current item for menu Points */
	item_table[2].cur_item = points_group_ind;
}
void navto_points_esc(void)
{
	for(uint8_t i = 0; i < MEMORY_SUBPOINTS; i++) {
		distance_old[i] = 0;
	}		// reset saved points values
	current_menu = M_MAIN;			//M_NAVIGATION;
}
//------------------------------NAV TO POINTS MENU END----------------------------
//----------------------------------------------------------------------
//----------------------------------POINTS MENU--------------------------------
void draw_points(void)
{
	for(uint8_t i = 0; i < (MEMORY_POINT_GROUPS + BEACON_POINT_GROUPS); i++)							//calculate saved memory points
		{
			pp_points_menu[i * MEMORY_SUBPOINTS]->exist_flag = 0;			//clear sub-point 0
			for(uint8_t j = 1; j < MEMORY_SUBPOINTS; j++)
			{
				if(pp_points_menu[i * MEMORY_SUBPOINTS + j]->exist_flag == 1) {
					pp_points_menu[i * MEMORY_SUBPOINTS]->exist_flag++;	//save to sub-point 0: 0, 28, 55, 83, 111, ...
				}
			}
		}

	draw_str_by_rows(0, 0, " N% POINTS SAVED i", &Font_7x9, CYAN,BLACK);

	row = get_current_item();
	for (uint8_t k = 1; k < (MEMORY_POINT_GROUPS + BEACON_POINT_GROUPS); k++)
	{
		sprintf(&string_buffer[k][0], "%2d", ((k < 7)? k: 7));
		draw_str_by_rows(0, 14+k*12, &string_buffer[k][0], &Font_7x9, CYAN,BLACK);
	}
	for (uint8_t k = 0; k < (MEMORY_POINT_GROUPS + BEACON_POINT_GROUPS); k++)		//draw points groups
	{
		(k < 7)? (sprintf(&string_buffer[k][0], " %7s  %1d  %2d", get_points_group_name(k), pp_points_menu[k * MEMORY_SUBPOINTS]->exist_flag,	//amount of saved sub-points
																	 pp_point_groups_menu[k]->index_in_flash)):
				 (sprintf(&string_buffer[k][0], " %7s  %1d  %2d", get_points_group_name(k), pp_points_menu[k * MEMORY_SUBPOINTS]->exist_flag,
				 	 	 	 	 	 	 	 	 	 	 	 	 	 pp_devices_menu[1 + k - MEMORY_POINT_GROUPS]->index_in_flash));
		if(k == row) draw_str_by_rows(21, 14+k*12, &string_buffer[k][0], &Font_7x9, YELLOW,BLACK);		//active points group
		else draw_str_by_rows(21, 14+k*12, &string_buffer[k][0], &Font_7x9, GREEN,BLACK);				//other points groups
	}
	draw_char(21, 14+row*12, *">", &Font_7x9, YELLOW,BLACK);
}
void points_esc(void)
{
	if(row < 7)
	{
		points_group_ind = row;
		(pp_points_menu[row * MEMORY_SUBPOINTS]->exist_flag)? (current_menu = M_NAVTO_POINTS): (current_menu = M_MAIN);
	}else
	{
		main_flags.current_device = row - MEMORY_POINT_GROUPS + 1;
		(pp_points_menu[row * MEMORY_SUBPOINTS]->exist_flag)? (current_menu = M_BEACONS): (current_menu = M_MAIN);
	}
}
void draw_show_points(void)
{
	main_flags.current_point_group = row;

	sprintf(&string_buffer[0][1], " %2d %7s points:", pp_points_menu[main_flags.current_point_group * MEMORY_SUBPOINTS]->exist_flag, get_points_group_name(main_flags.current_point_group));
	draw_str_by_rows(0, 0, &string_buffer[0][1], &Font_6x8, CYAN,BLACK);

	uint8_t k = 0;

	for(uint8_t i = 1; i < MEMORY_SUBPOINTS; i++)
	{
		if(pp_points_menu[main_flags.current_point_group * MEMORY_SUBPOINTS + i]->exist_flag == 1) {
			sprintf(&string_buffer[k][0], "%1dLatit : %ld", i, pp_points_menu[main_flags.current_point_group * MEMORY_SUBPOINTS + i]->latitude.as_integer);
		//sprintf(&string_buffer[k][0], "%1dLatit : %ld",i ,pp_points_menu[12]->latitude.as_integer);
			draw_str_by_rows(0, 8+k*11, &string_buffer[k][0], &Font_7x9, GREEN,BLACK);
			sprintf(&string_buffer[++k][0], "%1dLongit: %ld", i, pp_points_menu[main_flags.current_point_group * MEMORY_SUBPOINTS + i]->longitude.as_integer);
		//sprintf(&string_buffer[k][0], "%1dLatit : %ld",i ,pp_points_menu[12]->longitude.as_integer);
			draw_str_by_rows(0, 7+k*11, &string_buffer[k][0], &Font_7x9, YLWGRN,BLACK);
			if(++k > 14) i = MEMORY_SUBPOINTS;			//restrict to 14 lines
		}
	}
}

void draw_clear_group(void)
{
	if((pp_points_menu[main_flags.current_point_group * MEMORY_SUBPOINTS]->exist_flag) && (main_flags.current_point_group < 7))
	{
		fill_screen(BLACK);

		draw_str_by_rows(8, 1*18, "CLEAR THIS", &Font_11x18, CYAN,BLACK);
		draw_str_by_rows(3, 2*18, "GROUP WHITH", &Font_11x18, CYAN,BLACK);
		draw_str_by_rows(3, 3*18, "ALL POINTS?", &Font_11x18, YELLOW,BLACK);
		draw_str_by_rows(0, 4*18+8, "    OK?", &Font_11x18, ORANGE,BLACK);
		draw_str_by_rows(5, 5*18+16, "    or", &Font_11x18, CYAN,BLACK);
		draw_str_by_rows(0, 6*18+24, "    ESC", &Font_11x18, GREEN,BLACK);

		current_menu = M_CONFIRM_CLEARGROUP;
	}
	else current_menu = M_POINTS;
}

void confirm_clear_group(void)
{
	clear_points_group(main_flags.current_point_group);

	int8_t ind;
	for(uint8_t sub_point = 0; sub_point < MEMORY_SUBPOINTS; sub_point++)
	{
		ind = (main_flags.current_point_group * MEMORY_SUBPOINTS) + sub_point;
	   	pp_points_menu[ind]->exist_flag = 0;
	}
   	saved_group_load(main_flags.current_point_group);

	current_menu = M_POINTS;
}

//------------------------------MEMORY POINTS END----------------------------
//---------------------------------------------------------------------------
//-----------------------------SETTINGS MENU---------------------------------
void draw_settings(void)
{
	draw_str_by_rows(0, 0, "     SETTINGS     ", &Font_7x9, CYAN,BLACK);
//	todo? (p_settings_menu->) instead of (settings_copy_menu.)
	sprintf(&string_buffer[0][0], " Device:%1d/%1d", settings_copy_menu.device_number, settings_copy_menu.devices_on_air);	//this_device);
	sprintf(&string_buffer[1][0], " SprFctr %02d", settings_copy_menu.spreading_factor);		//LORA_SPREADING_FACTOR);

//	sprintf(&string_buffer[2][0], " Region %d", (800 + p_freq_region_values[settings_copy_menu.freq_region_opt]));
	sprintf(&string_buffer[2][0], " CodRate4/%d", p_coding_rate_values[settings_copy_menu.coding_rate_opt]);
	sprintf(&string_buffer[3][0], " Channel %2d", settings_copy_menu.freq_channel);
	sprintf(&string_buffer[4][0], " TxPower%3d", p_tx_power_values[settings_copy_menu.tx_power_opt]);	//settings_copy_menu.tx_power_opt);
	sprintf(&string_buffer[5][0], " TimZone %2d", settings_copy_menu.time_zone_hour);
	sprintf(&string_buffer[6][0], " TimeOut%3d", settings_copy_menu.timeout_threshold);
	sprintf(&string_buffer[7][0], " Fence  %3d", settings_copy_menu.fence_threshold);
	row = get_current_item();
	for (uint8_t k = 0; k < 8; k++)
	{
		if(k == row) draw_str_by_rows(3, 10+k*19, &string_buffer[k][0], &Font_11x18, YELLOW,BLACK);
		else draw_str_by_rows(3, 10+k*19, &string_buffer[k][0], &Font_11x18, GREEN,BLACK);
	}

	draw_char(3, 10+row*19, *">", &Font_11x18, YELLOW,BLACK);
}

void draw_set_settings(void)
	{
	draw_str_by_rows(0, 0, "  MODIFY THE VALUE", &Font_7x9, CYAN,BLACK);

	sprintf(&string_buffer[0][0], " Device:%1d/%1d", settings_copy_menu.device_number, settings_copy_menu.devices_on_air);	//this_device);
	sprintf(&string_buffer[1][0], " SprFctr %02d", settings_copy_menu.spreading_factor);		//LORA_SPREADING_FACTOR);

	sprintf(&string_buffer[2][0], " CR_opt   %d", settings_copy_menu.coding_rate_opt);
	sprintf(&string_buffer[3][0], " Channel %2d", settings_copy_menu.freq_channel);
	sprintf(&string_buffer[4][0], " TxPower%3d", p_tx_power_values[settings_copy_menu.tx_power_opt]);	//settings_copy_menu.tx_power_opt);
	sprintf(&string_buffer[5][0], " TimZone %2d", settings_copy_menu.time_zone_hour);
	sprintf(&string_buffer[6][0], " TimOut %3d", settings_copy_menu.timeout_threshold);
	sprintf(&string_buffer[7][0], " Fence  %3d", settings_copy_menu.fence_threshold);
//		int8_t row = get_current_item();
	for (uint8_t k = 0; k < 8; k++)
	{
		if(k == row) draw_str_by_rows(3, 10+k*19, &string_buffer[k][0], &Font_11x18, CYAN,BLACK);
		else draw_str_by_rows(3, 10+k*19, &string_buffer[k][0], &Font_11x18, GREEN,BLACK);
	}

	draw_char(3, 10+row*19, *">", &Font_11x18, CYAN,BLACK);
}
//---------------------------------SETTINGS SET-----------------------------------
	/*********************DEVICE NUMBER************************/
	void set_device_number_up(void)
	{
		if (settings_copy_menu.device_number == settings_copy_menu.devices_on_air)
		{
			settings_copy_menu.device_number = DEVICE_NUMBER_FIRST;

			if (settings_copy_menu.devices_on_air == DEVICE_NUMBER_LAST)
			{
				settings_copy_menu.devices_on_air = DEVICE_NUMBER_FIRST + 2;
			}else {
				settings_copy_menu.devices_on_air++;
			}
		}else {
			settings_copy_menu.device_number++;
		}
	}
	void set_device_number_down(void)
	{
		if (settings_copy_menu.device_number == DEVICE_NUMBER_FIRST)
		{
			if (settings_copy_menu.devices_on_air == (DEVICE_NUMBER_FIRST + 2))
			{
				settings_copy_menu.devices_on_air = DEVICE_NUMBER_LAST;
			}else {
				settings_copy_menu.devices_on_air--;
			}

			settings_copy_menu.device_number = settings_copy_menu.devices_on_air;
		}else {
			settings_copy_menu.device_number--;
		}

	}
	void set_device_number_ok(void)
	{
	    if ((settings_copy_menu.device_number != this_device) | (settings_copy_menu.devices_on_air != p_settings_menu->devices_on_air))
	    {
	        flag_settings_changed = 1;
//	    	settings_save(&settings_copy_menu);
//	    	settings_load();
	    	main_flags.display_status = 1;		//otherwise it shut off
	    }
	    current_menu = M_SETTINGS;
	}
	void set_device_number_esc(void)
	{
	    settings_copy_menu.device_number = this_device;   			//exit with no save, reset values
	    settings_copy_menu.devices_on_air = p_settings_menu->devices_on_air;
	    current_menu = M_SETTINGS;
	}
	/*********************SPREADING FACTOR************************/
	void set_spreading_factor_up(void)
	{
		(settings_copy_menu.spreading_factor > 11)? (settings_copy_menu.spreading_factor = 7): settings_copy_menu.spreading_factor++;
	}
	void set_spreading_factor_down(void)
	{
		(settings_copy_menu.spreading_factor < 8)? (settings_copy_menu.spreading_factor = 12): settings_copy_menu.spreading_factor--;
	}
	void set_spreading_factor_ok(void)
	{
	    if (settings_copy_menu.spreading_factor != p_settings_menu->spreading_factor)
	    {
//	    	(settings_copy_menu.spreading_factor == 12)? serialPrint(set_pertriple_period, sizeof(set_pertriple_period)):
//	    												 serialPrint(set_persecond_period, sizeof(set_persecond_period));
	        flag_settings_changed = 1;
//	    	settings_save(&settings_copy_menu);
//	    	settings_load();
	    }
	    current_menu = M_SETTINGS;
	}
	void set_spreading_factor_esc(void)
	{
	    settings_copy_menu.spreading_factor = p_settings_menu->spreading_factor;   //exit no save, reset values
	    current_menu = M_SETTINGS;
	}
	/*********************CODING RATE************************/
	void set_coding_rate_up(void) {
		    if (settings_copy_menu.coding_rate_opt == CODING_RATE_LAST_OPTION)
		    {
		        settings_copy_menu.coding_rate_opt = CODING_RATE_FIRST_OPTION;
		    }else {
		        settings_copy_menu.coding_rate_opt++;
		    }
		}
		void set_coding_rate_down(void) {
		    if (settings_copy_menu.coding_rate_opt == CODING_RATE_FIRST_OPTION)
		    {
		        settings_copy_menu.coding_rate_opt = CODING_RATE_LAST_OPTION;
		    }else {
		        settings_copy_menu.coding_rate_opt--;
		    }
		}
		void set_coding_rate_ok(void) {
		    if (settings_copy_menu.coding_rate_opt != p_settings_menu->coding_rate_opt) {
		    	flag_settings_changed = 1;
//		    	settings_save(&settings_copy_menu);
//		    	settings_load();
		    }
		    current_menu = M_SETTINGS;
		}
		void set_coding_rate_esc(void) {
		    settings_copy_menu.coding_rate_opt = p_settings_menu->coding_rate_opt;   //exit no save, reset value
		    current_menu = M_SETTINGS;
		}
	/******************************CHANNEL************************/
	void set_freq_channel_up(void) {
	    if (settings_copy_menu.freq_channel >= FREQ_CHANNEL_LAST)
	    {
	        settings_copy_menu.freq_channel = FREQ_CHANNEL_FIRST;
	    }else {
	        settings_copy_menu.freq_channel += 5;
	    }
	}
	void set_freq_channel_down(void) {
	    if (settings_copy_menu.freq_channel <= FREQ_CHANNEL_FIRST)
	    {
	        settings_copy_menu.freq_channel = FREQ_CHANNEL_LAST;
	    }else {
	        settings_copy_menu.freq_channel -= 5;
	    }
	}
	void set_freq_channel_ok(void) {
	    if (settings_copy_menu.freq_channel != p_settings_menu->freq_channel) {
	    	flag_settings_changed = 1;
//	    	settings_save(&settings_copy_menu);
//	    	settings_load();
	    }
	    current_menu = M_SETTINGS;
	}
	void set_freq_channel_esc(void) {
	    settings_copy_menu.freq_channel = p_settings_menu->freq_channel;   //exit no save, reset value
	    current_menu = M_SETTINGS;
	}
	/********************************POWER*******************************/
	void set_tx_power_up(void) {
	    if (settings_copy_menu.tx_power_opt == TX_POWER_LAST_OPTION)
	    {
	        settings_copy_menu.tx_power_opt = TX_POWER_FIRST_OPTION;
	    }else {
	        settings_copy_menu.tx_power_opt++;
	    }
	}
	void set_tx_power_down(void) {
	    if (settings_copy_menu.tx_power_opt == TX_POWER_FIRST_OPTION)
	    {
	        settings_copy_menu.tx_power_opt = TX_POWER_LAST_OPTION;
	    }else {
	        settings_copy_menu.tx_power_opt--;
	    }
	}
	void set_tx_power_ok(void) {
	    if (settings_copy_menu.tx_power_opt != p_settings_menu->tx_power_opt) {
	    	flag_settings_changed = 1;
//	    	settings_save(&settings_copy_menu);
//	    	settings_load();
	    }
	    current_menu = M_SETTINGS;
	}
	void set_tx_power_esc(void) {
	    settings_copy_menu.tx_power_opt = p_settings_menu->tx_power_opt;   //exit no save, reset value
	    current_menu = M_SETTINGS;
	}
	/*********************************TIMEOUT****************************/
	void set_timeout_up(void) {
		if (settings_copy_menu.timeout_threshold >= TIMEOUT_THRESHOLD_MAX)
		{
			settings_copy_menu.timeout_threshold = TIMEOUT_THRESHOLD_MIN;
		}else {
			settings_copy_menu.timeout_threshold += TIMEOUT_THRESHOLD_STEP;
		}
	}
	void set_timeout_down(void) {
		if (settings_copy_menu.timeout_threshold <= TIMEOUT_THRESHOLD_MIN)
		{
			settings_copy_menu.timeout_threshold = TIMEOUT_THRESHOLD_MAX;
		}else {
			settings_copy_menu.timeout_threshold -= TIMEOUT_THRESHOLD_STEP;
		}
	}
	void set_timeout_ok(void) {
	    if (settings_copy_menu.timeout_threshold != p_settings_menu->timeout_threshold) {
//	    	flag_settings_changed = 1;
	    	settings_save(&settings_copy_menu);
	       	settings_load();
	    }
	    current_menu = M_SETTINGS;
	}
	void set_timeout_esc(void) {
		settings_copy_menu.timeout_threshold = p_settings_menu->timeout_threshold;   //exit no save, reset value
	    current_menu = M_SETTINGS;
	}
	/*****************************FENCE**********************************/
	void set_fence_up(void) {
		if (settings_copy_menu.fence_threshold >= FENCE_THRESHOLD_MAX)
		{
			settings_copy_menu.fence_threshold = FENCE_THRESHOLD_MIN;
		}else {
			settings_copy_menu.fence_threshold += FENCE_THRESHOLD_STEP;
		}
	}
	void set_fence_down(void) {
		if (settings_copy_menu.fence_threshold <= FENCE_THRESHOLD_MIN)
		{
			settings_copy_menu.fence_threshold = FENCE_THRESHOLD_MAX;
		}else {
			settings_copy_menu.fence_threshold -= FENCE_THRESHOLD_STEP;
		}
	}
	void set_fence_ok(void) {
	    if (settings_copy_menu.fence_threshold != p_settings_menu->fence_threshold) {
//	    	flag_settings_changed = 1;
	    	settings_save(&settings_copy_menu);
	    	settings_load();
	    }
	    current_menu = M_SETTINGS;
	}
	void set_fence_esc(void) {
		settings_copy_menu.fence_threshold = p_settings_menu->fence_threshold;   //exit no save, reset value
	    current_menu = M_SETTINGS;
	}
	/****************************TIMEZONE*********************************/
	void set_timezone_up(void) {
		(settings_copy_menu.time_zone_hour > 11)? (settings_copy_menu.time_zone_hour = -12): settings_copy_menu.time_zone_hour++;
	}
	void set_timezone_down(void) {
		(settings_copy_menu.time_zone_hour < -11)? (settings_copy_menu.time_zone_hour = 12): settings_copy_menu.time_zone_hour--;
	}
	void set_timezone_ok(void) {
	    if(settings_copy_menu.time_zone_hour != p_settings_menu->time_zone_hour) {
//	        flag_settings_changed = 1;
	        settings_save(&settings_copy_menu);
	       	settings_load();
	    }
	    current_menu = M_SETTINGS;
	}
	void set_timezone_esc(void) {
		settings_copy_menu.time_zone_hour = p_settings_menu->time_zone_hour;
	    current_menu = M_SETTINGS;
	}
	/**************************CONFIRM SETTINGS*****************************/
void draw_confirm_settings(void)
{
    if (flag_settings_changed)
    {
    	sprintf(&string_buffer[1][0], "    SETTINGS     ");
    	sprintf(&string_buffer[2][0], "   HAS CHANGED   ");
   		sprintf(&string_buffer[3][0], "            ");
    	for (uint8_t k = 1; k < 4; k++) {
    		draw_str_by_rows(0, k*11, &string_buffer[k][0], &Font_7x9, GREEN,BLACK);
    	}

    	draw_str_by_rows(0, 4*11, " Press OK  ", &Font_11x18, YELLOW,BLACK);

   		draw_str_by_rows(0, 6*11, " REBOOT AND APPLY", &Font_7x9, GREEN,BLACK);

	   	draw_str_by_rows(0, 8*11, " Press ESC ", &Font_11x18, YELLOW,BLACK);

	    sprintf(&string_buffer[8][0], "  TO NOT SAVE ");
	    sprintf(&string_buffer[9][0], "   AND REBOOT ");
	    for (uint8_t k = 8; k < 10; k++) {
	    	draw_str_by_rows(0, (k+2)*11, &string_buffer[k][0], &Font_7x9, GREEN,BLACK);
	    }
    }else current_menu = M_MAIN;
}
void confirm_settings_reboot(void)
{
	fill_screen(BLACK);
	row = 4;
	draw_str_by_rows(0, row*18, " Saving...", &Font_11x18, YELLOW,BLACK);

    flag_settings_changed = 0;
   	settings_save(&settings_copy_menu);

    HAL_Delay(1000);
    NVIC_SystemReset();
}

void donot_save_settings(void)
{
	fill_screen(BLACK);

	row = 4;
	draw_str_by_rows(0, row*18, "Restoring..", &Font_11x18, YELLOW,BLACK);
//	settings_copy_menu = *p_settings_menu;   //reset to no changes state
	HAL_Delay(1000);
	NVIC_SystemReset();
}
//-----------------------------SETTINGS MENU END------------------------
//----------------------------------------------------------------------
//----------------------------- MENU ACTIONS------------------------
void draw_actions(void)
{
	draw_str_by_rows(0, 0, "     ACTIONS    ", &Font_7x9, CYAN,BLACK);

	sprintf(&string_buffer[0][0], " Power OFF");
	(pp_devices_menu[this_device]->emergency_flag)? sprintf(&string_buffer[1][0], " Emerge  on"): sprintf(&string_buffer[1][0], " Emerge off");

//	(pp_devices_menu[this_device]->antitheft_flag)?     sprintf(&string_buffer[2][0], " ATheft  on"): sprintf(&string_buffer[2][0], " ATheft off");
	if(pp_devices_menu[this_device]->antitheft_flag == 0) sprintf(&string_buffer[2][0], " ATheft off");
	else if(p_settings_menu->spreading_factor == 12)
	{
		if(pp_devices_menu[this_device]->antitheft_flag == 2) sprintf(&string_buffer[2][0], " ATheft1 on");
		else if(pp_devices_menu[this_device]->antitheft_flag == 1) sprintf(&string_buffer[2][0], " ATheft2 on");
	}
	else sprintf(&string_buffer[2][0], " ATheft  on");

//	(pp_devices_menu[this_device]->bcntohalt_flag)?    sprintf(&string_buffer[3][0], " BeaconHalt"): sprintf(&string_buffer[3][0], " BeaconLive");
	if(pp_devices_menu[this_device]->bcntohalt_flag == 0) sprintf(&string_buffer[3][0], " BeaconLive");
	else if(p_settings_menu->spreading_factor == 12)
	{
		if(pp_devices_menu[this_device]->bcntohalt_flag == 2) sprintf(&string_buffer[3][0], " tBcn1 halt");
		else if(pp_devices_menu[this_device]->bcntohalt_flag == 1) sprintf(&string_buffer[3][0], " tBcn2 halt");
	}
	else sprintf(&string_buffer[3][0], " BeaconHalt");

//	(pp_devices_menu[this_device]->beeper_flag)?    sprintf(&string_buffer[6][0], " Beeper  on"): sprintf(&string_buffer[6][0], " Beeper off");
	if(pp_devices_menu[this_device]->beeper_flag == 0) sprintf(&string_buffer[4][0], " Beeper off");
	else if(p_settings_menu->spreading_factor == 12)
    {//SF12 only: invert flags to transmit in the slot, beacon can get: slot1 for beacon2, slot2 for beacon1
		if(pp_devices_menu[this_device]->beeper_flag == 2) sprintf(&string_buffer[4][0], " Beeper1 on");
		else if(pp_devices_menu[this_device]->beeper_flag == 1) sprintf(&string_buffer[4][0], " Beeper2 on");
	}
	else sprintf(&string_buffer[4][0], " Beeper  on");

	sprintf(&string_buffer[5][0], " Del points");
	sprintf(&string_buffer[6][0], " SetDefault");

	sprintf(&string_buffer[7][0], " BindingBcn");
//	(pp_devices_menu[this_device]->flwtrek_flag)? sprintf(&string_buffer[7][0], " FlwTrek on"): sprintf(&string_buffer[7][0], " FlwTrekOff");

	row = get_current_item();
	for (uint8_t k = 0; k < 8; k++)
	{
		if(k == row) draw_str_by_rows(3, 10+k*19, &string_buffer[k][0], &Font_11x18, YELLOW,BLACK);
		else {
			draw_str_by_rows(3, 10+k*19, &string_buffer[k][0], &Font_11x18, GREEN,BLACK);
		}
	}

	draw_char(3, 10+row*19, *">", &Font_11x18, YELLOW,BLACK);
}

void power_long(void)
{
	if(current_menu == M_ACTIONS)
	{
		pp_devices_menu[this_device]->emergency_flag = 1;
		set_current_item(1);
	}

	if (current_menu == M_POINTS) {	//otherwise if some point saved, halt after BTN_PWR_LONG immediately
		memory_subpoint_ind[main_flags.current_point_group] = 0;
		main_flags.current_point_group = 0;
	}

	return_from_power_menu = current_menu;
	current_menu = M_ACTIONS;

	shortBeeps(2);					//notice power_long and set emergency_flag
}

void actions_ok(void)	//non standard implementation: switch the current item and do the action
{
	switch (get_current_item())
	{
		case M_ACTIONS_I_POWER_OFF:
			for(uint8_t i = 0; i < MEMORY_POINT_GROUPS; i++)
			{
				if(flag_group_has_changed[i])	points_group_save(i);
			}
			led_w_on();
			HAL_Delay(50);
			release_power();

			break;

		case M_ACTIONS_I_EMERGENCY:
			(pp_devices_menu[this_device]->emergency_flag == 0)?
					(pp_devices_menu[this_device]->emergency_flag = 1):
					(pp_devices_menu[this_device]->emergency_flag = 0);
			break;

		case M_ACTIONS_I_ANTITHEFT:		//toggle_alarm();
			if(!pp_devices_menu[this_device]->bcntohalt_flag && !pp_devices_menu[this_device]->beeper_flag)
			{
				if(p_settings_menu->spreading_factor == 12)
				{
					if(pp_devices_menu[this_device]->antitheft_flag == 0) pp_devices_menu[this_device]->antitheft_flag = 2;			//0x10
					else if(pp_devices_menu[this_device]->antitheft_flag == 2) pp_devices_menu[this_device]->antitheft_flag = 1;	//0x01
					else pp_devices_menu[this_device]->antitheft_flag = 0;															//0x00
				}
				else
				{
					(pp_devices_menu[this_device]->antitheft_flag == 0)?
					(pp_devices_menu[this_device]->antitheft_flag = 1):
					(pp_devices_menu[this_device]->antitheft_flag = 0);
				}
			}
			break;

		case M_ACTIONS_I_BCNHALT:	//toggle_gather();
			if(!pp_devices_menu[this_device]->antitheft_flag &&	!pp_devices_menu[this_device]->beeper_flag)
			{
				if(p_settings_menu->spreading_factor == 12)
				{
					if(pp_devices_menu[this_device]->bcntohalt_flag == 0) pp_devices_menu[this_device]->bcntohalt_flag = 2;			//0x10
					else if(pp_devices_menu[this_device]->bcntohalt_flag == 2) pp_devices_menu[this_device]->bcntohalt_flag = 1;	//0x01
					else pp_devices_menu[this_device]->bcntohalt_flag = 0;															//0x00
				}
				else
				{
					(pp_devices_menu[this_device]->bcntohalt_flag == 0)?
					(pp_devices_menu[this_device]->bcntohalt_flag = 1):
					(pp_devices_menu[this_device]->bcntohalt_flag = 0);
				}
			}
			break;

		case M_ACTIONS_I_BEEPER:	//toggle_trigger();
			if(!pp_devices_menu[this_device]->antitheft_flag &&	!pp_devices_menu[this_device]->bcntohalt_flag)
			{
				if(p_settings_menu->spreading_factor == 12)
				{
					if(pp_devices_menu[this_device]->beeper_flag == 0) pp_devices_menu[this_device]->beeper_flag = 2;		//0x10
					else if(pp_devices_menu[this_device]->beeper_flag == 2) pp_devices_menu[this_device]->beeper_flag = 1;	//0x01
					else pp_devices_menu[this_device]->beeper_flag = 0;														//0x00
				}
				else
				{
					(pp_devices_menu[this_device]->beeper_flag == 0)?
					(pp_devices_menu[this_device]->beeper_flag = 1):
					(pp_devices_menu[this_device]->beeper_flag = 0);
				}
			}
			break;

		case M_ACTIONS_I_ERASE_POINTS:
			current_menu = M_ERASE_POINTS;
			break;

		case M_ACTIONS_I_SET_DEFAULTS:
			current_menu = M_CONFIRM_RESTORING;
			break;

		case M_ACTIONS_I_FLWTREK:	//initial set in init_gnss() of gnss.c
			current_menu = M_BINDING;
//			(pp_devices_menu[this_device]->flwtrek_flag == 0)?
//					(pp_devices_menu[this_device]->flwtrek_flag = 1):
//					(pp_devices_menu[this_device]->flwtrek_flag = 0);
			break;
		default:
			break;
	}
}

void actions_esc(void)
{
	if (current_menu == M_ACTIONS) return_from_power_menu = M_MAIN;
	reset_current_item_in_menu(M_ACTIONS);
	current_menu = return_from_power_menu;
}

void draw_erase_points(void)
{
	sprintf(&string_buffer[1][0], "   ARE YOU SURE  ");
	sprintf(&string_buffer[2][0], "   TO ERASE ALL  ");
	sprintf(&string_buffer[3][0], "   SAVED POINTS  ");
	sprintf(&string_buffer[4][0], "    AND SAVED    ");
	sprintf(&string_buffer[5][0], "  DEVICE POINTS? ");
	for (uint8_t k = 1; k < 6; k++) {
		draw_str_by_rows(0, k*11, &string_buffer[k][0], &Font_7x9, CYAN,BLACK);
	}

	draw_str_by_rows(0, 7*11, "  YES (OK) ", &Font_11x18, YELLOW,BLACK);
	draw_str_by_rows(0, 10*11, "  NO (ESC) ", &Font_11x18, GREEN,BLACK);
}
void confirm_erase_points(void)
{
	erase_point_groups();
	erase_saved_devices();

	for(uint8_t i = 0; i < 96; i++)	//<56 for groups only, +40 for devices
	{
	   	pp_points_menu[i]->exist_flag = 0;
	}
	fill_screen(BLACK);

	row = 4;
	draw_str_by_rows(0, row*17-1, " Erasing...", &Font_11x18, YELLOW,BLACK);
    HAL_Delay(300);
	current_menu = M_ACTIONS;
}

void draw_restore_defaults(void)
{
	sprintf(&string_buffer[1][0], "   TO RESTORE    ");
	sprintf(&string_buffer[2][0], "    DEFAULT      ");
	sprintf(&string_buffer[3][0], "    SETTINGS     ");
	for (uint8_t k = 1; k < 4; k++) {
		draw_str_by_rows(0, k*11, &string_buffer[k][0], &Font_7x9, CYAN,BLACK);
	}

	draw_str_by_rows(0, 5*11, "Press OK to", &Font_11x18, YELLOW,BLACK);

	draw_str_by_rows(0, 7*11, "RESTORE AND REBOOT", &Font_7x9, GREEN,BLACK);
	draw_str_by_rows(0, 8*11, "CALIBRATE COMPASS!", &Font_7x9, RED,BLACK);

	draw_str_by_rows(0, 10*11, " Press ESC ", &Font_11x18, YELLOW,BLACK);
	draw_str_by_rows(0, 12*11, "CALL MENU ACTIONS ", &Font_7x9, GREEN,BLACK);
}
void confirm_settings_restore(void)
{
	fill_screen(BLACK);

	row = 4;
	draw_str_by_rows(0, row*18, "Restoring..", &Font_11x18, YELLOW,BLACK);

	settings_save_default(p_settings_menu);

    HAL_Delay(1000);
    NVIC_SystemReset();
}

void draw_binding(void)
{
	if(main_flags.fix_valid == p_settings_menu->devices_on_air)
	{
		if(main_flags.binding_sf == 12 && main_flags.binding_device > 2) main_flags.binding_device = 1;

		draw_str_by_rows(36, 15, "BIND", &Font_11x18, CYAN,BLACK);

		sprintf(&string_buffer[0][0], "DEVICE <%d>", main_flags.binding_device);
		sprintf(&string_buffer[1][0], "CH%02d <SF%2d>",
//				p_settings_menu->freq_channel, p_settings_menu->spreading_factor);
				p_settings_menu->freq_channel, main_flags.binding_sf);

		if(this_device == main_flags.binding_device)
		{
			draw_str_by_rows(8, 2*19, &string_buffer[0][0], &Font_11x18, ORANGE,BLACK);
			draw_str_by_rows(3, 3*19, "THIS DEVICE", &Font_11x18, ORANGE,BLACK);
		}
		else
		{
			draw_str_by_rows(8, 2*19, &string_buffer[0][0], &Font_11x18, YELLOW,BLACK);
			draw_str_by_rows(3, 3*19, &string_buffer[1][0], &Font_11x18, YELLOW,BLACK);
		}

		if(main_flags.binding)
		{
			draw_str_by_rows(3, 4*19, "<=BINDING=>", &Font_11x18, ORANGE,BLACK);
		}
		else
		{
			draw_str_by_rows(5, 4*19, "    OK  ", &Font_11x18, YELLOW,BLACK);
			draw_str_by_rows(5, 5*19, "    or", &Font_11x18, CYAN,BLACK);
		}
	}
	else
	{
		draw_str_by_rows(25, 3*19, "NO GNSS", &Font_11x18, ORANGE,BLACK);
		draw_str_by_rows(36, 4*19, "FIXED", &Font_11x18, ORANGE,BLACK);
	}

	draw_str_by_rows(0, 6*19+4, "    ESC", &Font_11x18, GREEN,BLACK);
}
void confirm_binding(void)
{
	(main_flags.fix_valid == p_settings_menu->devices_on_air)? (main_flags.binding = 1): (current_menu = M_ACTIONS);
	if(this_device == main_flags.binding_device) main_flags.binding = 0;
}
void exit_binding(void)
{
	main_flags.binding = 0;
	current_menu = M_ACTIONS;
}
void device_up(void)
{
    if (main_flags.binding_device == p_settings_menu->devices_on_air)
     {
    	main_flags.binding_device = 1;
     }
    else main_flags.binding_device++;
}
void device_down(void)	//change to main_flags.binding_sf
{
	(main_flags.binding_sf == 11)? (main_flags.binding_sf = 12): (main_flags.binding_sf = 11);
//    if (main_flags.binding_device == 1)
//    {
//    	main_flags.binding_device = p_settings_menu->devices_on_air;
//    }
//    else main_flags.binding_device--;
}
