armor66/LoRa-E77-GNSS/E77-128x160/Core/Src/timer_it.c

#include "main.h"
#include "gpio.h"
#include "timer_it.h"
#include "tim.h"
#include "buttons.h"
#include "bit_band.h"
#include "menu.h"
#include "settings.h"
#include "lrns.h"
#include "e77radio.h"
#include "radio.h"
#include "gnss.h"		//for trek points
#include "compass.h"

int8_t pattern_index = 0;
int8_t long_beep_ones = 0;

uint8_t *p_tx_power_values_tim;

struct settings_struct *p_settings_tim;
struct devices_struct **pp_devices_tim;

void timer_it_init(void)
{
/*URS: Update request source
 * 0: Any of the following events generate an update interrupt or DMA request if enabled:
 * – Counter overflow/underflow
 * – Setting the UG bit
 * 1: Only counter overflow/underflow generates an update interrupt or DMA request if enabled:
 * no need to clear interrupt when CNT is reinitialized by software using the UG bit in TIMx_EGR register
*/
	TIM1->CR1 |= TIM_CR1_URS;
	TIM2->CR1 |= TIM_CR1_URS;
	TIM16->CR1 |= TIM_CR1_URS;
//	TIM17->CR1 |= TIM_CR1_URS;

	p_tx_power_values_tim = get_tx_power_values();
	p_settings_tim = get_settings();
	pp_devices_tim = get_devices();
}
const uint8_t timeslot_pattern[2][103] =
//PLmax=13(11+CRC), SF11, CR3(4/7), preamble=12, CRC_OFF, Air-Time = 627(+16?):357mS measured RxDone2Tx(should be 373mS)
//	| PVT|Slot1 OnRxDone time <650mS		+357mS|Slot2 OnTxDone time <650mS		  | PVT|Slot3					   | draw menu|
//	|----|-------------------------|---------|----|-------------------------|---------|----|-------------------------|---------|--
//	0 50 100mS	                             1000 1100mS							  2000 2100								 3000
  {{0,1, 2,0,0,0,0,0,0,0,0,0,0,0,0,3,4,5,4,5,4,1, 2,0,0,0,0,0,0,0,0,0,0,0,0,3,4,5,4,5,//4,1, 2,0,0,0,0,0,0,0,0,0,0,0,0,3,4,5,4,7,4,6 };
//	| PVT|Slot3					   | draw menu|PVT|Slot4					| draw menu|PVT|Slot5					 | draw menu|
//	|----|-------------------------|---------|----|-------------------------|---------|----|-------------------------|---------|--
//	2000 2100mS								 3000 3100mS							  4000 4100mS							   5000mS
	4,1, 2,0,0,0,0,0,0,0,0,0,0,0,0,3,4,5,4,5,4,1, 2,0,0,0,0,0,0,0,0,0,0,0,0,3,4,5,4,5,4,1, 2,0,0,0,0,0,0,0,0,0,0,0,0,3,4,5,4,5,4,1 },

//PLmax=13(CRC), SF12, CR3(4/7), preamble=8, CRC_ON, Air-Time = 1122(+33?):345mS measured RxDone2Tx (1150-1155=-5 !exceed!)
// PPS	 |Slot1 		AIR time 1122mS		PPS 		| draw menu|  |Slot2 		 PPS   		AIR time 1122mS      | draw menu|
//	|----|-----------------------------------|----|-----|-------------|---------------|----|-------------------------|---------|
//	0 50 100mS	                             1000		1250mS						  2000				    	  	2750	   3000
   {0,1, 2,0,0,0,0,0,0,0,0,0,0,0,0,0,6,0,0,0,0,0, 0,0,0,3,4,5,4,5,4,1,2,0,0,0,0,0,0,0,0,0, 0,0,0,0,6,0,0,0,0,0,0,0,0,3,4,5,4,5,4,1 }};
//	|----|---------------------------|------------------|-------------|----------------------------|-----------------|---------|
//	0 50 100mS	                    +700     		   +1150mS	     1600				  	      +700				+1150	   3000
//PLmax=3(CRC), SF12, CR3(4/7), preamble=8, CRC_ON, Air-Time = 663(+33?)=696(gap does not make sense here)
static void restartPattern(void)
{
	getADC_sensors();
	clear_fix_data(p_settings_tim->device_number);
	timer1_stop();
	timer1_start();
	main_flags.time_slot = 0;			// from TIM1_IRQ case: 2
	main_flags.time_slot_timer_ovf = 0;
	main_flags.pps_synced = 0;
	led_blue_on();			//led_blue_off on case 1 (50ms)
	led_red_on();			//as pattern_started on PPS
	if(!main_flags.nav_pvt_ram_flag)
	{
		shortBeeps(2);
	}
	get_ds3231time();
}

void TIM1_UP_IRQHandler(void)
{
	TIM1->SR &= ~TIM_SR_UIF;                    //clear interrupt
	if(!main_flags.scanRadioFlag)
    {
		main_flags.time_slot_timer_ovf++;
		(p_settings_tim->spreading_factor == 12)? (pattern_index = 1): (pattern_index = 0);
		switch (timeslot_pattern[pattern_index][main_flags.time_slot_timer_ovf])
		{
		case 0:			//do nothing
			break;

		case 1:			//50mS
			if(p_settings_tim->spreading_factor == 12) main_flags.time_slot++;
			if(p_settings_tim->devices_on_air == main_flags.time_slot)	//if PPS did not come, but cycle completed + 50mS
			{
				restartPattern();
				break;
			}
			if(p_settings_tim->spreading_factor != 12) main_flags.time_slot++;
//clear what should be received or not in this slot after draw menu has finished
			if(p_settings_tim->device_number != main_flags.time_slot)
			{
				clear_fix_data(main_flags.time_slot);

				pp_devices_tim[main_flags.time_slot]->antitheft_flag = 0;
				pp_devices_tim[main_flags.time_slot]->bcntohalt_flag = 0;
			}

//set receive LORA_IQ_NORMAL in other time slot whilst transmitting with LORA_IQ_INVERTED has occurred
//(for [p_settings_tim->device_number == 3] only)
//only if (p_settings_tim->spreading_factor == 12) && (pp_devices_tim[3]->beeper_flag != time_slot)
			if(main_flags.transmit_iq_inverted_flag)
			{
				main_flags.transmit_iq_inverted_flag = 0;

				Radio.SetRxConfig(MODEM_LORA, LORA_BANDWIDTH, p_settings_tim->spreading_factor,
				p_settings_tim->coding_rate_opt, 0, p_settings_tim->preamble, LORA_SYMBOL_TIMEOUT,
				LORA_FIX_LENGTH_PAYLOAD_ON,	BUFFER_AIR_SIZE, CRC_ON, 0, 0, LORA_IQ_NORMAL, false);	//CRC, Hop, HopPer, IQ, single mode
			}


			if(main_flags.pps_synced) led_green_on();	//to shorten it, instead of PPS start
			led_blue_off();								//led_blue_on new pattern or PPS IRQ
			led_red_off();								//after new pattern started
			break;

		case 2:			//100mS
			main_flags.rx_crc_error = 0;
			led_green_off();			//if PVT not received or half pattern on SF12
			if(main_flags.long_beeps)
			{
				main_flags.long_beeps_flag = 1;
				led_w_on();
			}
			if(main_flags.display_status)	//moved here to show when SF12 also
			{
				main_flags.endRX_2_TX = (uint16_t)TIM17->CNT;		//save interval from RX-end to TX-start
				timer17_stop();		//stop here to reload/clear
			}

			if(main_flags.time_slot == p_settings_tim->device_number)	//this device, never met in case SF12(slots 1 and 2 only)
			{	//if this device doesn't get gnss fix via uart 100mS after PPS, delay for full pattern time
				if(!pp_devices_tim[p_settings_tim->device_number]->valid_fix_flag) main_flags.fix_valid--;
				if(main_flags.fix_valid > 0)	//do not transmit if no GNSS FIX
				{
//					if(main_flags.display_status)	//moved up
//					{
//						main_flags.endRX_2_TX = (uint16_t)TIM17->CNT;		//save interval from RX-end to TX-start
//						timer17_stop();
//					}
					if(main_flags.binding) shortBeeps(1);
					main_flags.permit_actions = 0;
					led_red_on();					//start transmitting, end by case 3 (OnTxDone)
					set_transmit_data();			//State = TX_START;
				}
				else	//for SF11
				{
					main_flags.locked = 0;	//save time to ds3231 next time fix valid occurs
					main_flags.fix_valid = 0;			//just to avoid negative values
				}
			}
			else//if(time_slot != p_settings_tim->device_number)	other devices:
			{
				if(p_settings_tim->spreading_factor == 12)	//for device3 only
				{
					if(!pp_devices_tim[p_settings_tim->device_number]->valid_fix_flag) main_flags.fix_valid--;

					if(main_flags.fix_valid > 0)	//do not transmit if no GNSS FIX
					{
/* transmit on demand if flag has set(choose to which beacon send) with LORA_IQ_INVERTED */
						if((pp_devices_tim[3]->antitheft_flag == main_flags.time_slot) ||
								(pp_devices_tim[3]->bcntohalt_flag == main_flags.time_slot) ||
								(pp_devices_tim[3]->beeper_flag == main_flags.time_slot))	//1 for beacon2 or 2 for beacon1
						{	//beeper_flags inverted to transmit in the slot, beacon can get: slot1 for beacon2, slot2 for beacon1
							main_flags.permit_actions = 0;
							main_flags.transmit_iq_inverted_flag = 1;	//set transmit LORA_IQ_INVERTED
							Radio.SetTxConfig(MODEM_LORA, p_tx_power_values_tim[p_settings_tim->tx_power_opt], 0,
								LORA_BANDWIDTH,	p_settings_tim->spreading_factor, p_settings_tim->coding_rate_opt,
								p_settings_tim->preamble, LORA_FIX_LENGTH_PAYLOAD_ON, CRC_ON, 0, 0, LORA_IQ_INVERTED, TX_TIMEOUT_VALUE);
							led_red_on();			//start transmitting(SF12), end by case 3
							set_transmit_data();	//transmit flags and time only with buffer_to_transmit = 3
						}
						else Radio.RxBoosted(0);	//start to receive SF12 on slot 1 or 2
					}
					else	//for SF12
					{
						main_flags.locked = 0;	//save time to ds3231 next time fix valid occurs
						main_flags.fix_valid = 0;			//just to avoid negative values
					}
				}
				else Radio.RxBoosted(0);			//start to receive if SF != 12

/*manage (pp_devices_tim[time_slot]->beeper_flag) on it own slot only, if beeper_flag received previously in this slot)*/
				if(pp_devices_tim[main_flags.time_slot]->beeper_flag)
				{
					led_w_on();
					pp_devices_tim[main_flags.time_slot]->beeper_flag = 0;
					long_beep_ones = 1;	//set here to finish on case 3 after starts here only
				}
			}
			break;

		case 3:				//check if remote devices on the air, draw menu items
			led_red_off();	//650ms after OnRxDone
			if(main_flags.time_slot != p_settings_tim->device_number)	//for receiver slot only
			{
				if(pp_devices_tim[p_settings_tim->device_number]->valid_fix_flag &&		//host gnss data is valid (implemented in rx_to_devices())
						pp_devices_tim[main_flags.time_slot]->beacon_traced &&			//timeout_threshold is set & valid data has received once
						!pp_devices_tim[main_flags.time_slot]->valid_fix_flag)			//not valid data received now
				{	//do decrement beacon_traced in lrns.c, except when beep flag sent to one of two beacons in beacon mode (SF12)
					if(!((p_settings_tim->spreading_factor == 12) &&
							((pp_devices_tim[3]->antitheft_flag == main_flags.time_slot) ||
							(pp_devices_tim[3]->bcntohalt_flag == main_flags.time_slot) ||
							(pp_devices_tim[3]->beeper_flag == main_flags.time_slot))))
					{
						check_traced(main_flags.time_slot);
					}
					//do beeps if beacon was traced and lost gnss fix
					if(pp_devices_tim[main_flags.time_slot]->beacon_traced * (p_settings_tim->devices_on_air - 1) < 14) shortBeeps(1);
					if(pp_devices_tim[main_flags.time_slot]->beacon_lost)						//if beacon_traced became zero
					{
						//save beacon trace if it was traced and no validFixFlag[main_flags.time_slot] for timeout_threshold
						lost_device_save(main_flags.time_slot);
						main_flags.current_point_group = 0;		//to prevent accidental erase saved device point by long pressed BTN_ESC
						//start long beep on next case 2 в слоте того устройства, которое пропало
						pp_devices_tim[main_flags.time_slot]->beeper_flag = 1;
						//shortBeeps(main_flags.time_slot);
					}
				}
			}
/*******************IF THERE IS ANY OF BEEP FLAGS****************************************/
			(p_settings_tim->timeout_threshold || p_settings_tim->fence_threshold)? mute_off(): mute_on();
			if(main_flags.short_beeps && !main_flags.short_beeps_flag && !main_flags.long_beeps)
			{
				main_flags.short_beeps_flag = 1;
				led_w_on();
			}
			if(long_beep_ones)
			{
				led_w_off();
				long_beep_ones = 0;
			}
			if(main_flags.long_beeps && main_flags.long_beeps_flag)
			{
				if(p_settings_tim->spreading_factor != 12)	//SF12 use case 6 instead
				{
					main_flags.long_beeps--;
					led_w_off();
				}
			}
/******************IF MENU NAVIGATION ENTERED*****************************************/
			if(main_flags.find_nearest_trekpoint_flag)
			{
				__disable_irq();
				find_nearest_trekpoint();
			}
			while(main_flags.find_nearest_trekpoint_flag);		//wait and __enable_irq(); after that
/***********************************************************/
			read_north();
			if(!main_flags.pps_synced)	//before any PPS interrupt occurs
			{
				main_flags.elapsed_sec++;
				if(main_flags.laps_afoot) main_flags.lapsTime++;
			}
			main_flags.update_screen = 1;
			main_flags.permit_actions = 1;		//process buttons here after
			break;

		case 4:
			if(main_flags.short_beeps_flag && main_flags.short_beeps)
			{
				led_w_off();
				main_flags.short_beeps--;
			}
			break;

		case 5:
			if(main_flags.short_beeps && main_flags.short_beeps_flag)	//(main_flags.short_beeps < 3))
			{
				led_w_on();
			}
			break;

		case 6:	//for SF12 to shorten long beeps only
			if(main_flags.long_beeps && main_flags.long_beeps_flag)
			{
				main_flags.long_beeps--;
				led_w_off();
			}
//			if(main_flags.display_status)	// to calculate Rx timeout
//			{
//				timer17_stop();
//				main_flags.endRX_2_TX = (uint16_t)TIM17->CNT;		//save interval from RX-end to TX-start
//			}
			break;

		default:
			break;
		}
    }
	else timer1_scanRadio_handle();	// if(scanRadioFlag)
}

void TIM2_IRQHandler(void)					//Scan buttons interval	void TIM3_IRQHandler(void)
{
	TIM2->SR &= ~TIM_SR_UIF;                //clear interrupt
//	led_red_on();
	if (main_flags.buttons_scanned == 0)	//if not scanned yet
	{
		main_flags.button_code = scan_button(main_flags.processing_button);
		if (main_flags.button_code)			//perhaps get rid off the buttons_scanned and clear button_code in main.c/while (1)
		{
			main_flags.buttons_scanned = 1;
		}
	}
}

void TIM16_IRQHandler(void)
{
	TIM16->SR &= ~TIM_SR_UIF;               //clear interrupt
	timer16_stop();
	main_flags.current_point_group = 0;
}
