armor66/LoRa-E77-GNSS/Pogo-tBeacon/Core/Inc/bitmap.h

#ifndef BITMAP_H_
#define BITMAP_H_

// данный логотип расширением 128 на 27

const unsigned char logo[]=
{
0x02, 0x49, 0x24, 0x00, 0x00, 0x00, 0x00, 0x00, 0x00, 0x00, 0x00, 0x00, 0x00, 0x00, 0x00, 0x00,
0x02, 0x49, 0x24, 0x00, 0x00, 0x00, 0x00, 0x00, 0x00, 0x00, 0x00, 0x00, 0x00, 0x00, 0x00, 0x00,
0x02, 0x49, 0x24, 0x00, 0x00, 0x00, 0x00, 0x00, 0x00, 0x00, 0x00, 0x00, 0x00, 0x00, 0x00, 0x00,
0x0f, 0xff, 0xff, 0x00, 0x00, 0x00, 0x00, 0x00, 0x00, 0x00, 0x00, 0x00, 0x00, 0x00, 0x00, 0x00,
0x1f, 0xff, 0xff, 0x80, 0x00, 0x7c, 0x00, 0x3e, 0x78, 0x00, 0x00, 0x00, 0x00, 0x00, 0x00, 0x00,
0x5c, 0x19, 0x93, 0xe0, 0x03, 0xff, 0xf8, 0x7e, 0xfc, 0x00, 0x00, 0x00, 0x00, 0x00, 0x00, 0x00,
0xfc, 0x11, 0x13, 0xe0, 0x0f, 0xff, 0xf8, 0x3c, 0xe0, 0x00, 0x00, 0x00, 0x00, 0x00, 0x00, 0x00,
0x1c, 0x11, 0x13, 0x00, 0x3f, 0xff, 0xfc, 0x3d, 0xc0, 0x00, 0x00, 0x00, 0x00, 0x00, 0x00, 0x00,
0xfd, 0xe2, 0x13, 0xe0, 0x7f, 0x81, 0xfc, 0x3f, 0xc0, 0x00, 0x00, 0x00, 0x00, 0x00, 0x06, 0x00,
0xfd, 0x04, 0x13, 0xe0, 0x7f, 0x00, 0xfc, 0x3f, 0xc0, 0x00, 0x00, 0x06, 0x00, 0x00, 0xc6, 0x00,
0x1d, 0x38, 0xe3, 0x00, 0xff, 0x00, 0x78, 0x1f, 0xe0, 0x79, 0xb9, 0xff, 0xbc, 0x5d, 0xf3, 0x2e,
0xff, 0x29, 0x03, 0xe0, 0xff, 0x00, 0x00, 0x3f, 0xf0, 0xdf, 0xfb, 0xae, 0x6d, 0xfc, 0xe7, 0x7e,
0xfc, 0x6a, 0x73, 0xe1, 0xfe, 0x00, 0x00, 0x3c, 0xf8, 0xdd, 0x99, 0xce, 0x0c, 0xcc, 0xc7, 0x76,
0x1c, 0x32, 0x53, 0x01, 0xff, 0x00, 0x00, 0x3e, 0x7c, 0xcd, 0x98, 0xee, 0x6c, 0xcc, 0xc7, 0x76,
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
};

#endif /* BITMAP_H_ */
