armor66/LoRa-E77-GNSS/Pogo-tBeacon/Core/Src/gpio.c

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

/* Includes ------------------------------------------------------------------*/
#include "gpio.h"

/* USER CODE BEGIN 0 */
#include "bit_band.h"
//#include "stm32wle5xx.h"
/* USER CODE END 0 */

/*----------------------------------------------------------------------------*/
/* Configure GPIO                                                             */
/*----------------------------------------------------------------------------*/
/** Configure pins as
        * Analog
        * Input
        * Output
        * EVENT_OUT
        * EXTI
*/
void MX_GPIO_Init(void)
{

  GPIO_InitTypeDef GPIO_InitStruct = {0};

  /* GPIO Ports Clock Enable */
  __HAL_RCC_GPIOB_CLK_ENABLE();
  __HAL_RCC_GPIOA_CLK_ENABLE();
  __HAL_RCC_GPIOC_CLK_ENABLE();

  /*Configure GPIO pin Output Level */
  HAL_GPIO_WritePin(GPIOB, LED_B_Pin|BUZZ_Pin|LED_G_Pin|SW_OUT_Pin
                          |CS_Pin, GPIO_PIN_RESET);

  /*Configure GPIO pin Output Level */
  HAL_GPIO_WritePin(GPIOA, LED_R_Pin|RF_CTRL1_Pin|RF_CTRL2_Pin|LED_W_Pin
                          |DC_Pin|RST_Pin, GPIO_PIN_RESET);

  /*Configure GPIO pin Output Level */
  HAL_GPIO_WritePin(HOLD_GPIO_Port, HOLD_Pin, GPIO_PIN_RESET);

  /*Configure GPIO pin : PtPin */
  GPIO_InitStruct.Pin = BTN_3_Pin;
  GPIO_InitStruct.Mode = GPIO_MODE_IT_FALLING;
  GPIO_InitStruct.Pull = GPIO_PULLUP;
  HAL_GPIO_Init(BTN_3_GPIO_Port, &GPIO_InitStruct);

  /*Configure GPIO pins : PBPin PBPin */
  GPIO_InitStruct.Pin = LED_B_Pin|LED_G_Pin;
  GPIO_InitStruct.Mode = GPIO_MODE_OUTPUT_OD;
  GPIO_InitStruct.Pull = GPIO_PULLUP;
  GPIO_InitStruct.Speed = GPIO_SPEED_FREQ_LOW;
  HAL_GPIO_Init(GPIOB, &GPIO_InitStruct);

  /*Configure GPIO pins : PBPin PBPin PBPin */
  GPIO_InitStruct.Pin = BUZZ_Pin|SW_OUT_Pin|CS_Pin;
  GPIO_InitStruct.Mode = GPIO_MODE_OUTPUT_PP;
  GPIO_InitStruct.Pull = GPIO_NOPULL;
  GPIO_InitStruct.Speed = GPIO_SPEED_FREQ_LOW;
  HAL_GPIO_Init(GPIOB, &GPIO_InitStruct);

  /*Configure GPIO pins : PAPin PAPin */
  GPIO_InitStruct.Pin = BTN_1_Pin|BTN_2_Pin;
  GPIO_InitStruct.Mode = GPIO_MODE_IT_FALLING;
  GPIO_InitStruct.Pull = GPIO_PULLUP;
  HAL_GPIO_Init(GPIOA, &GPIO_InitStruct);

  /*Configure GPIO pin : PtPin */
  GPIO_InitStruct.Pin = PPS_Pin;
  GPIO_InitStruct.Mode = GPIO_MODE_IT_RISING;
  GPIO_InitStruct.Pull = GPIO_PULLDOWN;
  HAL_GPIO_Init(PPS_GPIO_Port, &GPIO_InitStruct);

  /*Configure GPIO pin : PtPin */
  GPIO_InitStruct.Pin = LED_R_Pin;
  GPIO_InitStruct.Mode = GPIO_MODE_OUTPUT_OD;
  GPIO_InitStruct.Pull = GPIO_PULLUP;
  GPIO_InitStruct.Speed = GPIO_SPEED_FREQ_LOW;
  HAL_GPIO_Init(LED_R_GPIO_Port, &GPIO_InitStruct);

  /*Configure GPIO pins : PAPin PAPin */
  GPIO_InitStruct.Pin = RF_CTRL1_Pin|RF_CTRL2_Pin;
  GPIO_InitStruct.Mode = GPIO_MODE_OUTPUT_PP;
  GPIO_InitStruct.Pull = GPIO_NOPULL;
  GPIO_InitStruct.Speed = GPIO_SPEED_FREQ_HIGH;
  HAL_GPIO_Init(GPIOA, &GPIO_InitStruct);

  /*Configure GPIO pins : PAPin PAPin PAPin */
  GPIO_InitStruct.Pin = LED_W_Pin|DC_Pin|RST_Pin;
  GPIO_InitStruct.Mode = GPIO_MODE_OUTPUT_PP;
  GPIO_InitStruct.Pull = GPIO_NOPULL;
  GPIO_InitStruct.Speed = GPIO_SPEED_FREQ_LOW;
  HAL_GPIO_Init(GPIOA, &GPIO_InitStruct);

  /*Configure GPIO pin : PtPin */
  GPIO_InitStruct.Pin = HOLD_Pin;
  GPIO_InitStruct.Mode = GPIO_MODE_OUTPUT_PP;
  GPIO_InitStruct.Pull = GPIO_NOPULL;
  GPIO_InitStruct.Speed = GPIO_SPEED_FREQ_LOW;
  HAL_GPIO_Init(HOLD_GPIO_Port, &GPIO_InitStruct);

}

/* USER CODE BEGIN 2 */
void interrupt_init(void)
{
	TIM1->SR &= ~TIM_SR_UIF;                //clear update interrupt
	TIM1->DIER |= TIM_DIER_UIE;             //update interrupt enable
    NVIC_EnableIRQ(TIM1_UP_IRQn);

    TIM2->SR &= ~TIM_SR_UIF;                //clear update interrupt
    TIM2->DIER |= TIM_DIER_UIE;         //update interrupt enable
   	NVIC_EnableIRQ(TIM2_IRQn);

    TIM16->SR &= ~TIM_SR_UIF;            //clear update interrupt
    TIM16->DIER |= TIM_DIER_UIE;         //update interrupt enable
   	NVIC_EnableIRQ(TIM16_IRQn);

//    //PA4 - GPS PPS interrupt on rising edge
//    AFIO->EXTICR[0] |= AFIO_EXTICR1_EXTI2_PB;	//exti 2 source is port B
//    EXTI->RTSR |= EXTI_RTSR_TR2;				//interrupt 2 on rising edge
//    EXTI->IMR1 |= EXTI_IMR1_IM8;					//unmask interrupt 2
    NVIC_EnableIRQ(EXTI4_IRQn);             	//enable interrupt
//
//    //PB3 - DOWN/ESC button
//    AFIO->EXTICR[0] |= AFIO_EXTICR1_EXTI3_PB;	//exti 3 source is port B
//    EXTI->FTSR |= EXTI_FTSR_TR3;				//interrupt 3 on falling edge
    NVIC_EnableIRQ(EXTI3_IRQn);             	//enable interrupt
//
//    //PA1 - UP/OK button
//    AFIO->EXTICR[1] |= AFIO_EXTICR2_EXTI4_PB;	//exti 4 source is port B
//    EXTI->FTSR |= EXTI_FTSR_TR4;				//interrupt 4 on falling edge
    NVIC_EnableIRQ(EXTI1_IRQn);             	//enable interrupt
//
//    //PA0 - PWR button
//    AFIO->EXTICR[1] |= AFIO_EXTICR2_EXTI5_PB;   //exti 5 source is port B
//    EXTI->FTSR |= EXTI_FTSR_TR5;                //interrupt 5 on falling edge
    NVIC_EnableIRQ(EXTI0_IRQn);               //enable interrupt
//
//    EXTI->PR1 = (uint32_t)0x0007FFFF;            //clear all pending interrupts

    /* DMA1_Channel1_IRQn interrupt configuration */
//    HAL_NVIC_SetPriority(DMA1_Channel1_IRQn, 0, 0);
    NVIC_EnableIRQ(DMA1_Channel1_IRQn);
}

void enable_buttons_interrupts(void)
{
	BIT_BAND_PERI(EXTI->IMR1, EXTI_IMR1_IM3) = 1;		//unmask interrupt
//	EXTI->IMR1 |= EXTI_IMR1_IM5;
	BIT_BAND_PERI(EXTI->IMR1, EXTI_IMR1_IM1) = 1;		//unmask interrupt
//	EXTI->IMR1 |= EXTI_IMR1_IM1;
	BIT_BAND_PERI(EXTI->IMR1, EXTI_IMR1_IM0) = 1;		//unmask interrupt
//	EXTI->IMR1 |= EXTI_IMR1_IM0;
}

void disable_buttons_interrupts(void)
{
	BIT_BAND_PERI(EXTI->IMR1, EXTI_IMR1_IM3) = 0;		//mask interrupt
//	EXTI->IMR1 &= ~EXTI_IMR1_IM5;
	BIT_BAND_PERI(EXTI->IMR1, EXTI_IMR1_IM1) = 0;		//mask interrupt
//	EXTI->IMR1 &= ~EXTI_IMR1_IM1;
	BIT_BAND_PERI(EXTI->IMR1, EXTI_IMR1_IM0) = 0;		//mask interrupt
//	EXTI->IMR1 &= ~EXTI_IMR1_IM0;
}

void led_toggle_r(void){
	GPIOA->ODR ^= GPIO_ODR_OD5;
}
void led_red_on(void){
	GPIOA->BSRR = GPIO_BSRR_BR5;
}
void led_red_off(void){
	GPIOA->BSRR = GPIO_BSRR_BS5;
}
void led_toggle_g(void)
{
	GPIOB->ODR ^= GPIO_ODR_OD8;
}
void led_green_on(void){
	GPIOB->BSRR = GPIO_BSRR_BR8;
}
void led_green_off(void){
	GPIOB->BSRR = GPIO_BSRR_BS8;
}

void led_blue_on(void){
	GPIOB->BSRR = GPIO_BSRR_BR4;
}
void led_blue_off(void){
	GPIOB->BSRR = GPIO_BSRR_BS4;
}

void buzzer_toggle(void)
{
	GPIOB->ODR ^= GPIO_ODR_OD5;
}
void led_w_on(void){
	GPIOA->BSRR = GPIO_BSRR_BS9;	//LED
	GPIOB->BSRR = GPIO_BSRR_BS5;	//BUZZ
}
void led_w_off(void){
	GPIOA->BSRR = GPIO_BSRR_BR9;	//LED
	GPIOB->BSRR = GPIO_BSRR_BR5;	//BUZZ
}

void lcd_on(void){
	SW_OUT_GPIO_Port->BSRR = SW_OUT_Pin;
}
void lcd_off(void){
	SW_OUT_GPIO_Port->BSRR = (SW_OUT_Pin << 16);
}

void hold_power(void) {
    GPIOC->BSRR = GPIO_BSRR_BS13;
}
void release_power(void) {
    GPIOC->BSRR = GPIO_BSRR_BR13;
}

/* USER CODE END 2 */
