armor66/LoRa-E77-GNSS/E5-tBeacon/Core/Src/tim.c

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
/* Includes ------------------------------------------------------------------*/
#include "tim.h"

/* USER CODE BEGIN 0 */
#include "bit_band.h"
/* USER CODE END 0 */

TIM_HandleTypeDef htim1;
TIM_HandleTypeDef htim2;
TIM_HandleTypeDef htim16;
TIM_HandleTypeDef htim17;

/* TIM1 init function */
void MX_TIM1_Init(void)
{

  TIM_ClockConfigTypeDef sClockSourceConfig = {0};
  TIM_MasterConfigTypeDef sMasterConfig = {0};

  htim1.Instance = TIM1;
  htim1.Init.Prescaler = 47999;
  htim1.Init.CounterMode = TIM_COUNTERMODE_UP;
  htim1.Init.Period = 49;
  htim1.Init.ClockDivision = TIM_CLOCKDIVISION_DIV1;
  htim1.Init.RepetitionCounter = 0;
  htim1.Init.AutoReloadPreload = TIM_AUTORELOAD_PRELOAD_ENABLE;
  if (HAL_TIM_Base_Init(&htim1) != HAL_OK)
  {
    Error_Handler();
  }
  sClockSourceConfig.ClockSource = TIM_CLOCKSOURCE_INTERNAL;
  if (HAL_TIM_ConfigClockSource(&htim1, &sClockSourceConfig) != HAL_OK)
  {
    Error_Handler();
  }
  sMasterConfig.MasterOutputTrigger = TIM_TRGO_RESET;
  sMasterConfig.MasterOutputTrigger2 = TIM_TRGO2_RESET;
  sMasterConfig.MasterSlaveMode = TIM_MASTERSLAVEMODE_DISABLE;
  if (HAL_TIMEx_MasterConfigSynchronization(&htim1, &sMasterConfig) != HAL_OK)
  {
    Error_Handler();
  }
}
/* TIM2 init function */
void MX_TIM2_Init(void)
{

  TIM_ClockConfigTypeDef sClockSourceConfig = {0};
  TIM_MasterConfigTypeDef sMasterConfig = {0};

  htim2.Instance = TIM2;
  htim2.Init.Prescaler = 4799;
  htim2.Init.CounterMode = TIM_COUNTERMODE_UP;
  htim2.Init.Period = 99;
  htim2.Init.ClockDivision = TIM_CLOCKDIVISION_DIV1;
  htim2.Init.AutoReloadPreload = TIM_AUTORELOAD_PRELOAD_ENABLE;
  if (HAL_TIM_Base_Init(&htim2) != HAL_OK)
  {
    Error_Handler();
  }
  sClockSourceConfig.ClockSource = TIM_CLOCKSOURCE_INTERNAL;
  if (HAL_TIM_ConfigClockSource(&htim2, &sClockSourceConfig) != HAL_OK)
  {
    Error_Handler();
  }
  sMasterConfig.MasterOutputTrigger = TIM_TRGO_RESET;
  sMasterConfig.MasterSlaveMode = TIM_MASTERSLAVEMODE_DISABLE;
  if (HAL_TIMEx_MasterConfigSynchronization(&htim2, &sMasterConfig) != HAL_OK)
  {
    Error_Handler();
  }
}
/* TIM16 init function */
void MX_TIM16_Init(void)
{

  htim16.Instance = TIM16;
  htim16.Init.Prescaler = 47999;
  htim16.Init.CounterMode = TIM_COUNTERMODE_UP;
  htim16.Init.Period = 1499;
  htim16.Init.ClockDivision = TIM_CLOCKDIVISION_DIV1;
  htim16.Init.RepetitionCounter = 0;
  htim16.Init.AutoReloadPreload = TIM_AUTORELOAD_PRELOAD_DISABLE;
  if (HAL_TIM_Base_Init(&htim16) != HAL_OK)
  {
    Error_Handler();
  }
}
/* TIM17 init function */
void MX_TIM17_Init(void)
{

  htim17.Instance = TIM17;
  htim17.Init.Prescaler = 47999;
  htim17.Init.CounterMode = TIM_COUNTERMODE_UP;
  htim17.Init.Period = 65535;
  htim17.Init.ClockDivision = TIM_CLOCKDIVISION_DIV1;
  htim17.Init.RepetitionCounter = 0;
  htim17.Init.AutoReloadPreload = TIM_AUTORELOAD_PRELOAD_DISABLE;
  if (HAL_TIM_Base_Init(&htim17) != HAL_OK)
  {
    Error_Handler();
  }
}

void HAL_TIM_Base_MspInit(TIM_HandleTypeDef* tim_baseHandle)
{

  if(tim_baseHandle->Instance==TIM1)
  {
    /* TIM1 clock enable */
    __HAL_RCC_TIM1_CLK_ENABLE();
  /* USER CODE BEGIN TIM1_MspInit 1 */
    HAL_NVIC_SetPriority(TIM1_UP_IRQn, 0, 0);
    HAL_NVIC_EnableIRQ(TIM1_UP_IRQn);
  /* USER CODE END TIM1_MspInit 1 */
  }
  else if(tim_baseHandle->Instance==TIM2)
  {
    /* TIM2 clock enable */
    __HAL_RCC_TIM2_CLK_ENABLE();
  }
  else if(tim_baseHandle->Instance==TIM16)
  {
    /* TIM16 clock enable */
    __HAL_RCC_TIM16_CLK_ENABLE();
  }
  else if(tim_baseHandle->Instance==TIM17)
  {
    /* TIM17 clock enable */
    __HAL_RCC_TIM17_CLK_ENABLE();
  }
}

void HAL_TIM_Base_MspDeInit(TIM_HandleTypeDef* tim_baseHandle)
{

  if(tim_baseHandle->Instance==TIM1)
  {
    /* Peripheral clock disable */
    __HAL_RCC_TIM1_CLK_DISABLE();
  }
  else if(tim_baseHandle->Instance==TIM2)
  {
    /* Peripheral clock disable */
    __HAL_RCC_TIM2_CLK_DISABLE();
  }
  else if(tim_baseHandle->Instance==TIM16)
  {
    /* Peripheral clock disable */
    __HAL_RCC_TIM16_CLK_DISABLE();
  }
  else if(tim_baseHandle->Instance==TIM17)
  {
    /* Peripheral clock disable */
    __HAL_RCC_TIM17_CLK_DISABLE();
  }
}

/* USER CODE BEGIN 1 */
//Timer1 (time slot counter)
void timer1_start(void)
{
//    BIT_BAND_PERI(TIM1->CR1, TIM_CR1_CEN) = 1;
    TIM1->CR1 |= TIM_CR1_CEN;               //enable counter
}
void timer1_stop(void)
{
//	BIT_BAND_PERI(TIM1->CR1, TIM_CR1_CEN) = 0;
    TIM1->CR1 &= ~TIM_CR1_CEN;              //disable counter
//	TIM1->CNT = 0;
	TIM1->EGR = TIM_EGR_UG;                 //add {{0, at timeslot_pattern[0] and {0, at timeslot_pattern[1]

}

//Timer2 (buttons scan interval)
void timer2_start(void)
{
//    TIM2->DIER |= TIM_DIER_UIE;				//fixed with URS(Update request source)
//	BIT_BAND_PERI(TIM2->DIER, TIM_DIER_UIE) = 1;
//	BIT_BAND_PERI(TIM2->CR1, TIM_CR1_CEN) = 1;	//start timer
    TIM2->CR1 |= TIM_CR1_CEN;               	//enable counter
}

void timer2_stop(void)
{

//    TIM2->DIER &= ~TIM_DIER_UIE;				//fixed with URS(Update request source)
//	BIT_BAND_PERI(TIM2->CR1, TIM_CR1_CEN) = 0;	//stop  timer
    TIM2->CR1 &= ~TIM_CR1_CEN;             		//disable counter
//	TIM2->CNT = 0;
	TIM2->EGR = TIM_EGR_UG;
}

void timer16_start(uint16_t period)
{
	TIM16->ARR = period;
	TIM16->EGR = TIM_EGR_UG;					//to reload every start
    TIM16->CR1 |= TIM_CR1_CEN;               	//enable counter
}

void timer16_stop(void)
{
    TIM16->CR1 &= ~TIM_CR1_CEN;             		//disable counter
}

void timer17_start(void)
{
	TIM17->EGR = TIM_EGR_UG;					//to reload every start
    TIM17->CR1 |= TIM_CR1_CEN;               	//enable counter
}

void timer17_stop(void)
{
    TIM17->CR1 &= ~TIM_CR1_CEN;             	//disable counter
	TIM17->EGR = TIM_EGR_UG;					//clear for main_flags.endRX_2_TX
}
/* USER CODE END 1 */
